msgre/europe/docs/bottom/left_bottom.jpg

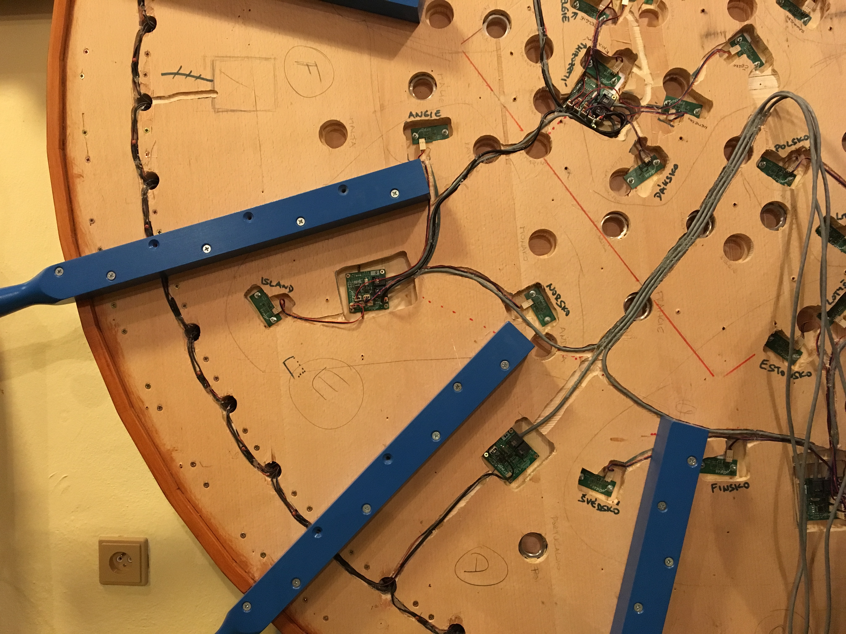
docs/bottom/left_bottom.jpg
