msgre/europe/docs/bottom/left_upper.jpg

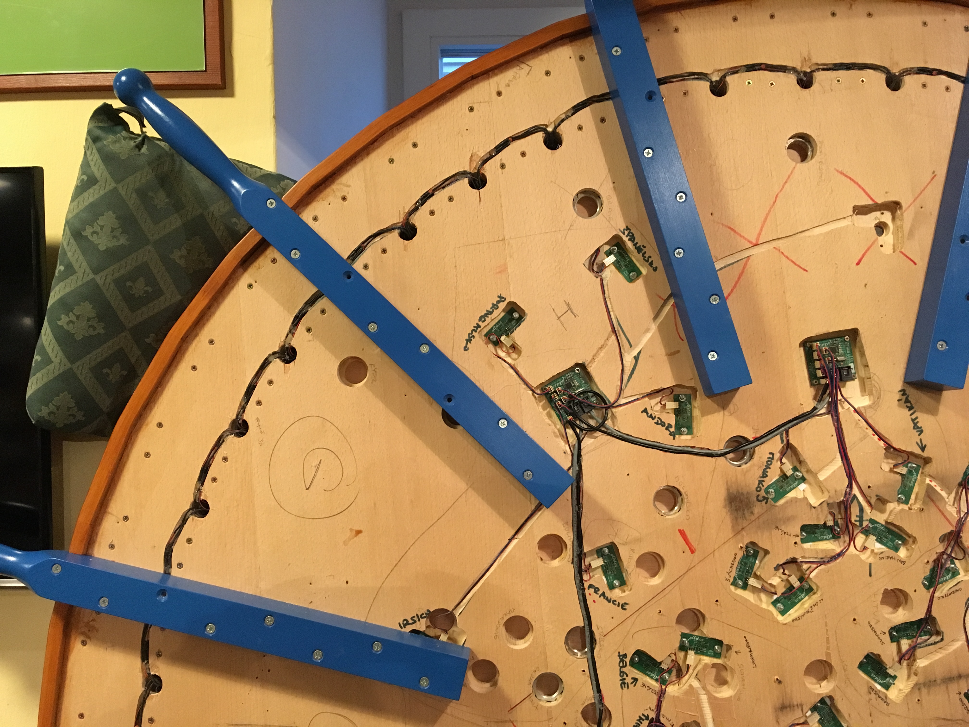
docs/bottom/left_upper.jpg
