msgre/europe/docs/bottom/right_upper.jpg

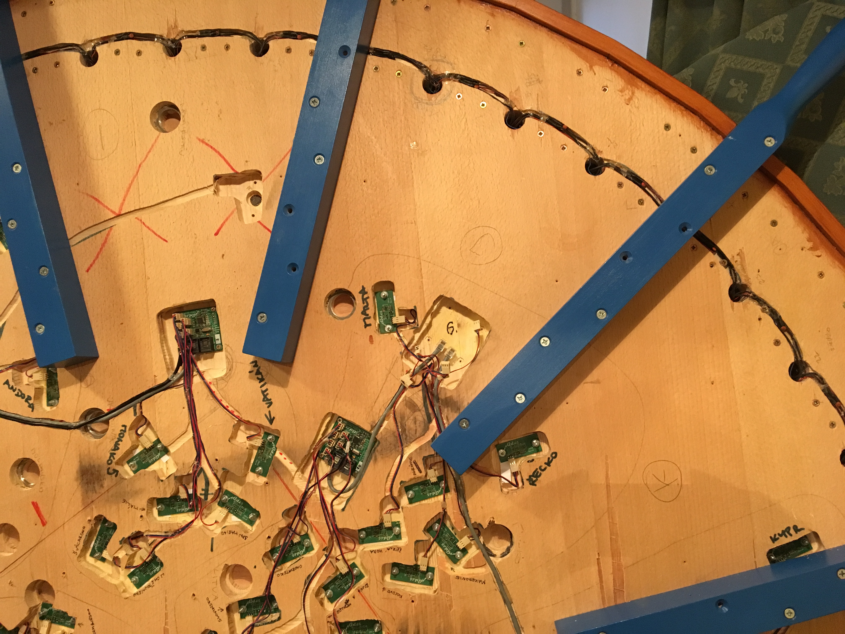
docs/bottom/right_upper.jpg
