msgre/europe/docs/bottom/whole.jpg

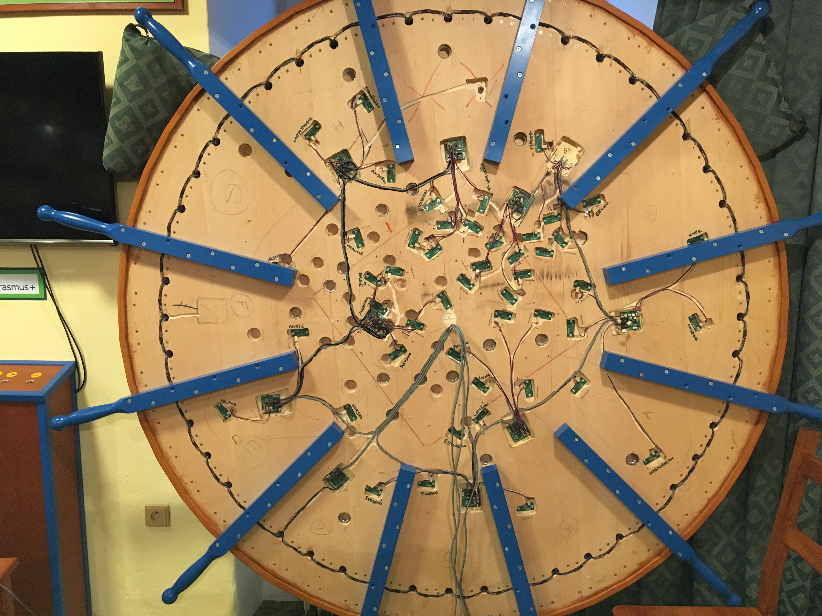
docs/bottom/whole.jpg
