msgre/europe/screenshots/01/01_uvod.png

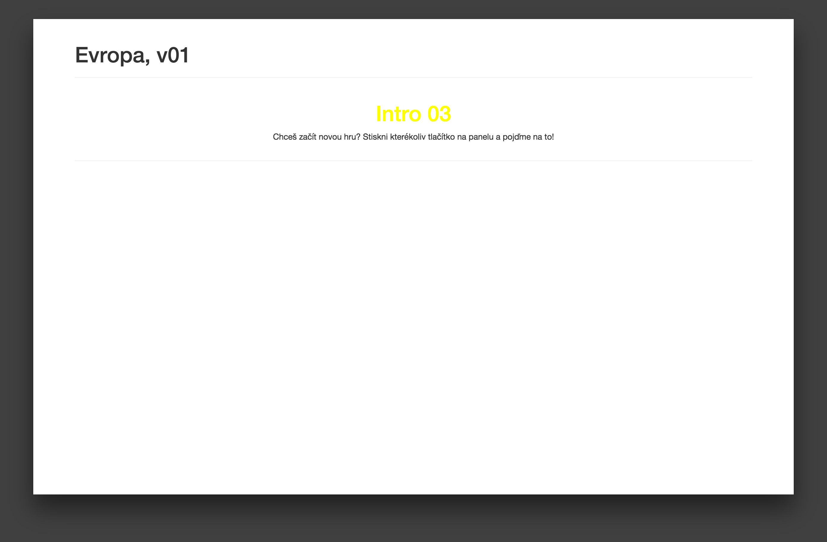
screenshots/01/01_uvod.png
