msgre/europe/screenshots/01/02_kategorie.png

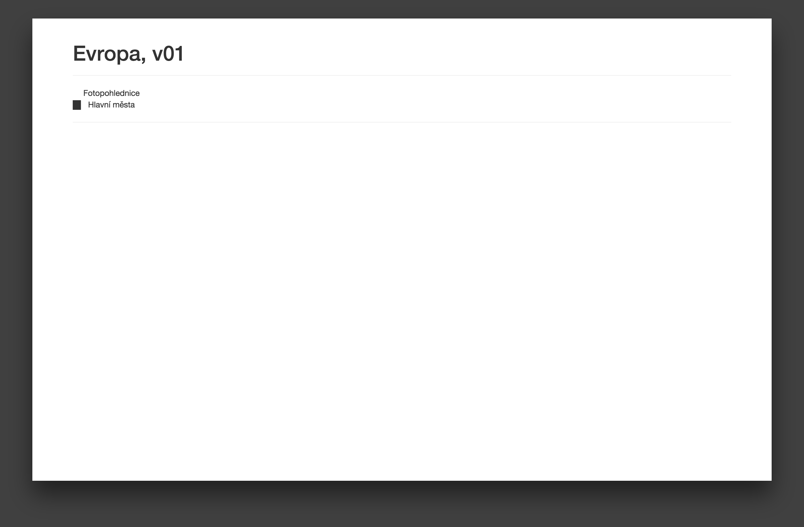
screenshots/01/02_kategorie.png
