msgre/europe/screenshots/01/04_hra.png

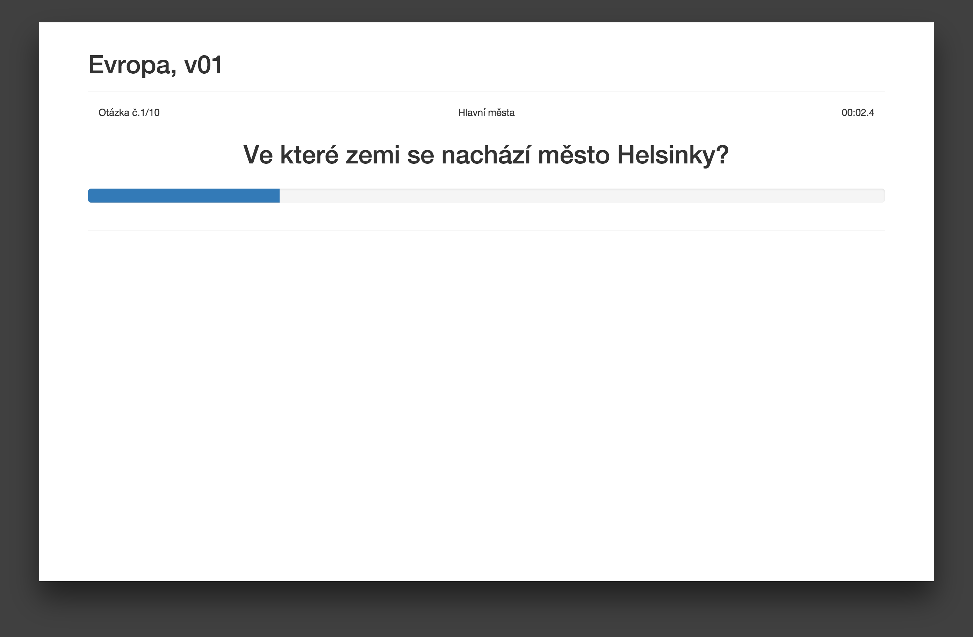
screenshots/01/04_hra.png
