msgre/europe/screenshots/01/05_rekord_1.png

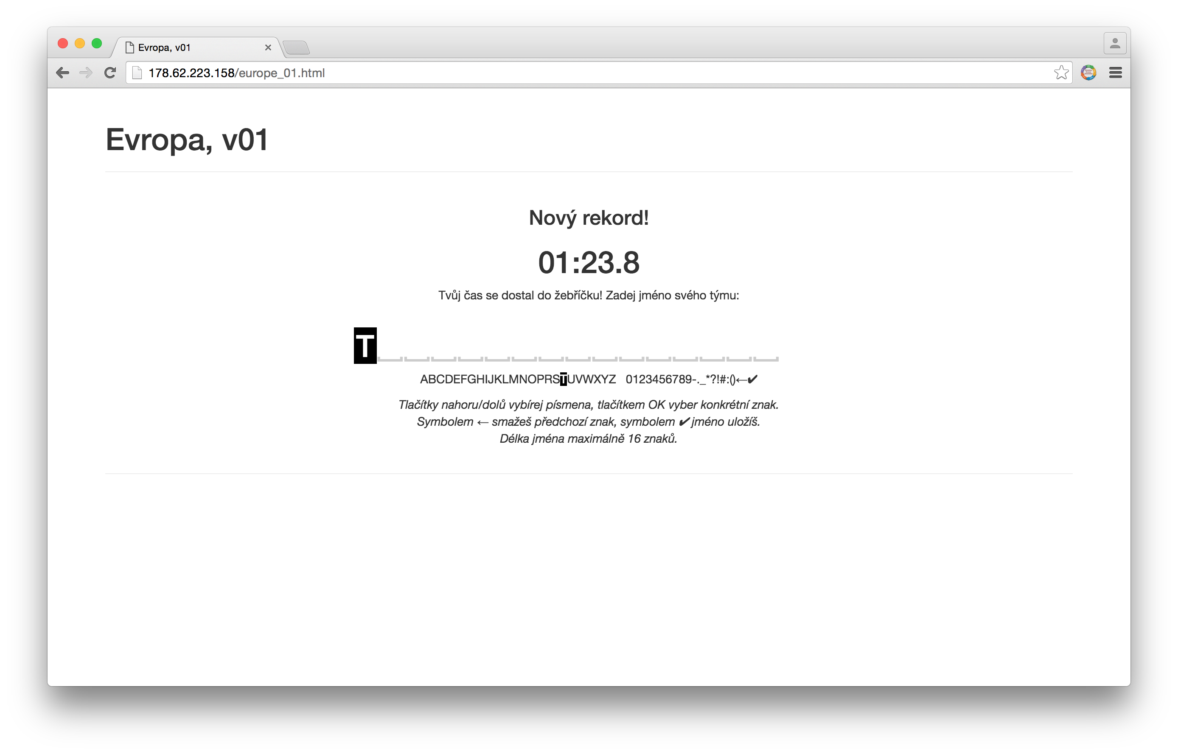
screenshots/01/05_rekord_1.png
