msgre/europe/screenshots/01/06_tabulky.png

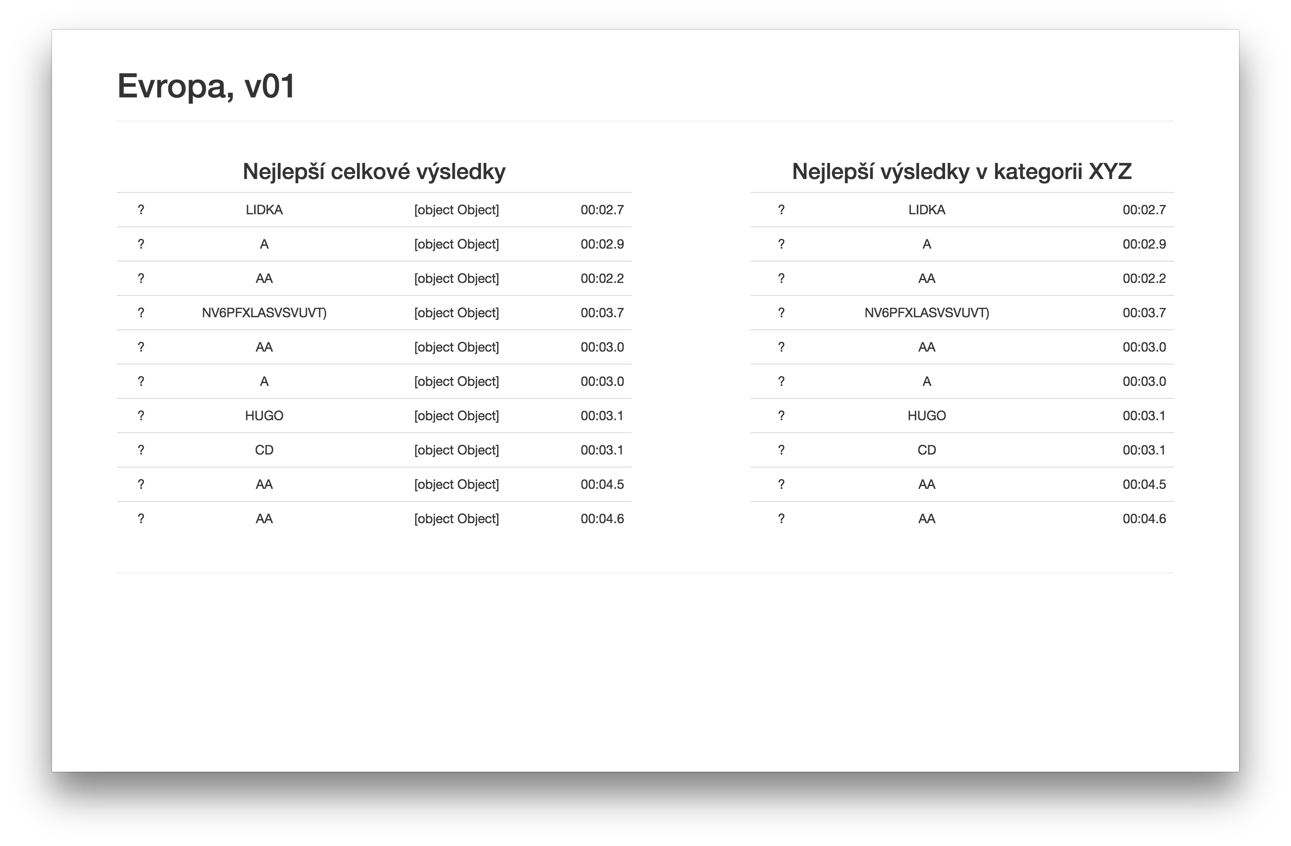
screenshots/01/06_tabulky.png
