msgre/europe/screenshots/02/evropa00.png

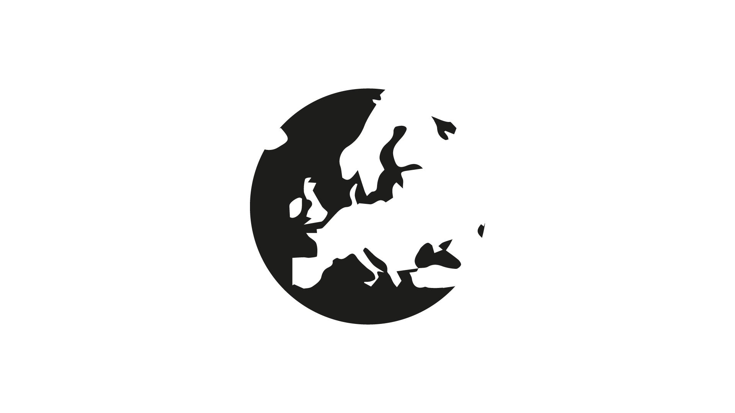
screenshots/02/evropa00.png
