msgre/europe/screenshots/02/evropa01.png

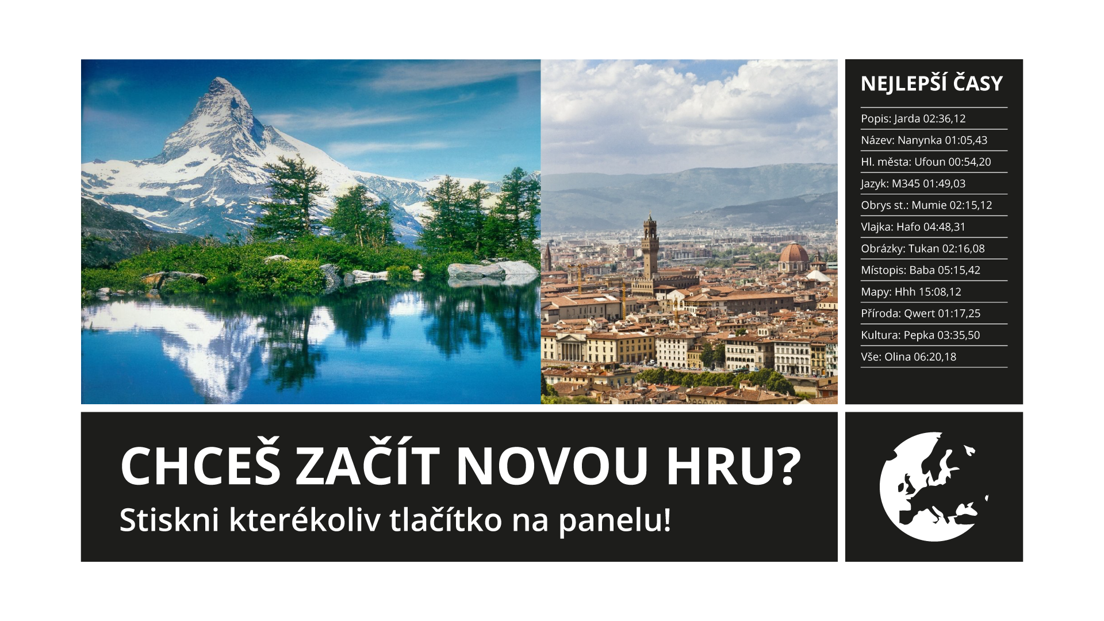
screenshots/02/evropa01.png
