msgre/europe/screenshots/02/evropa02.png

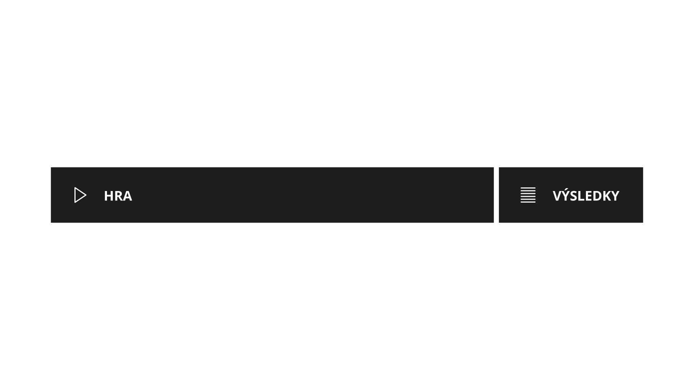
screenshots/02/evropa02.png
