msgre/europe/screenshots/02/evropa03.png

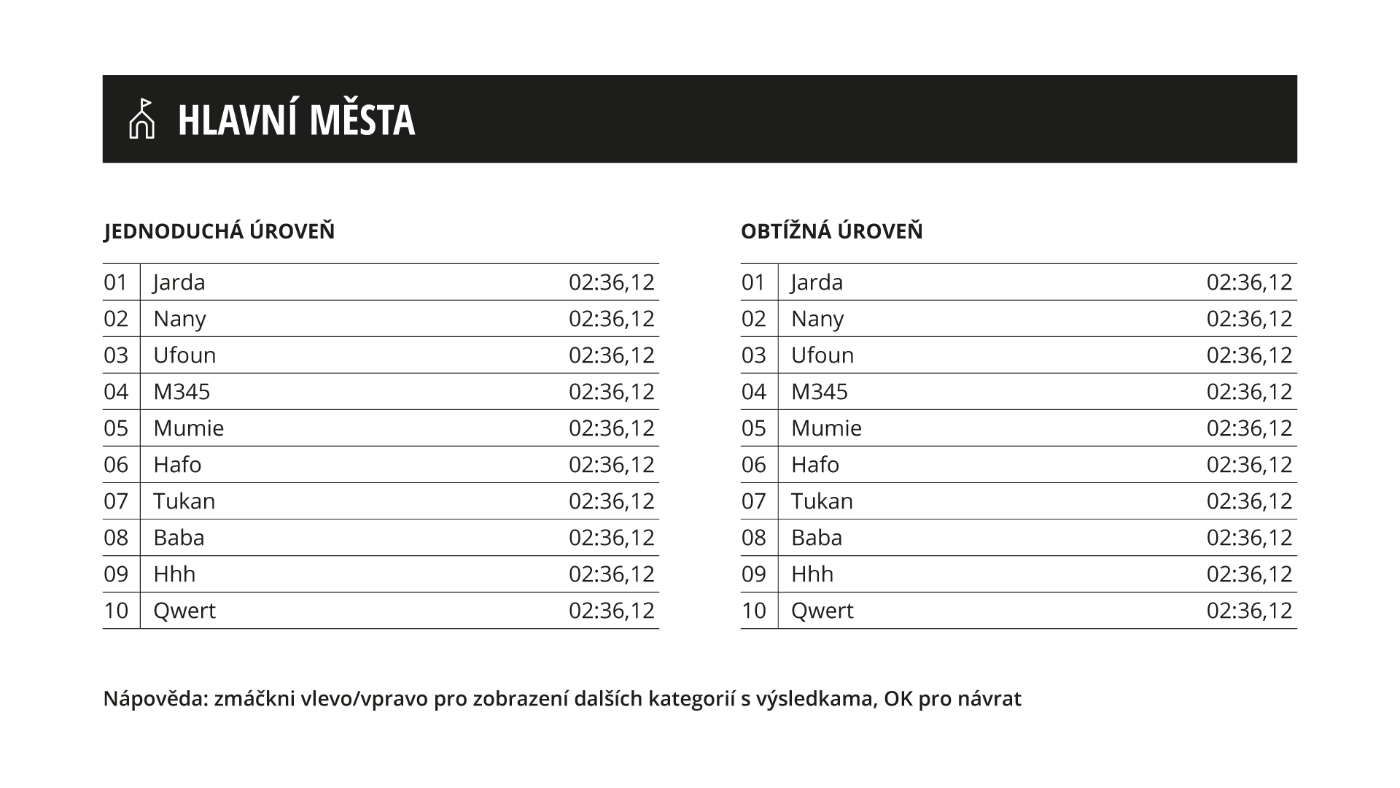
screenshots/02/evropa03.png
