msgre/europe/screenshots/02/evropa04.png

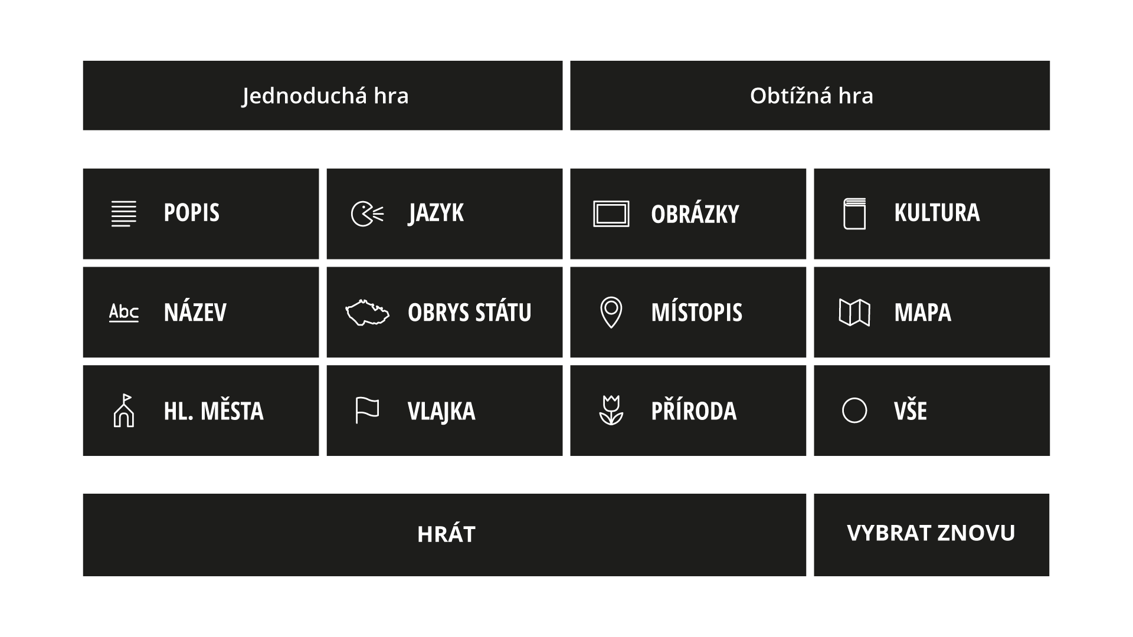
screenshots/02/evropa04.png
