msgre/europe/screenshots/02/evropa05a.png

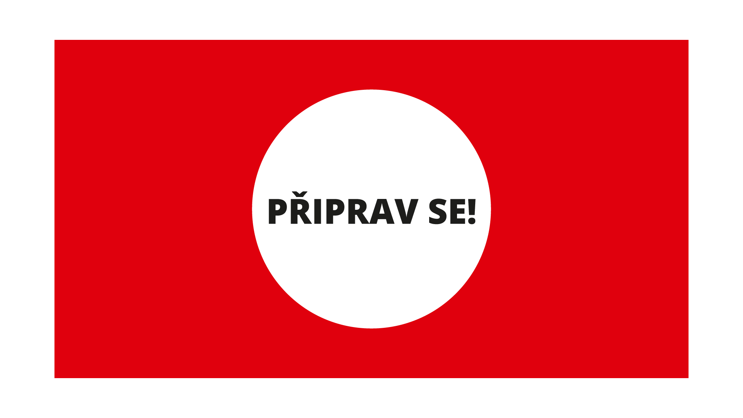
screenshots/02/evropa05a.png
