msgre/europe/screenshots/02/evropa05b.png

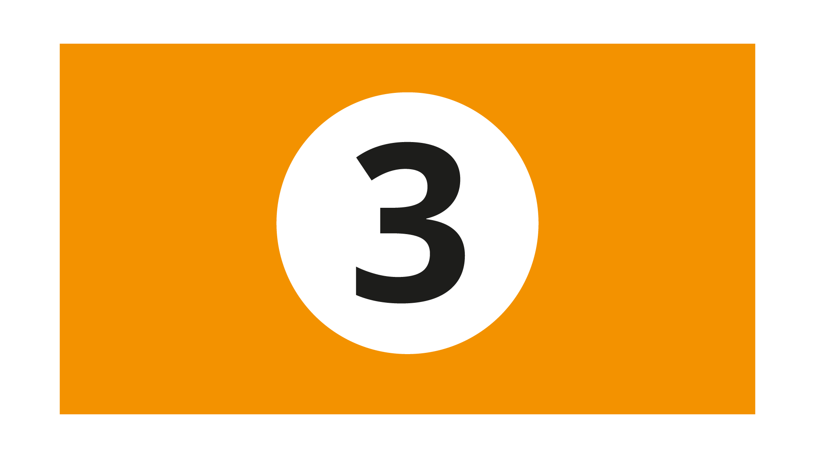
screenshots/02/evropa05b.png
