msgre/europe/screenshots/02/evropa06a.png

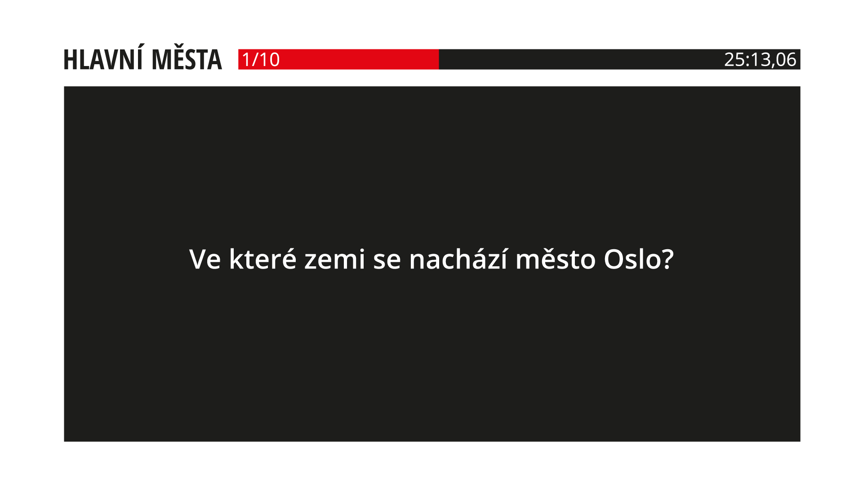
screenshots/02/evropa06a.png
