msgre/europe/screenshots/02/evropa06b.png

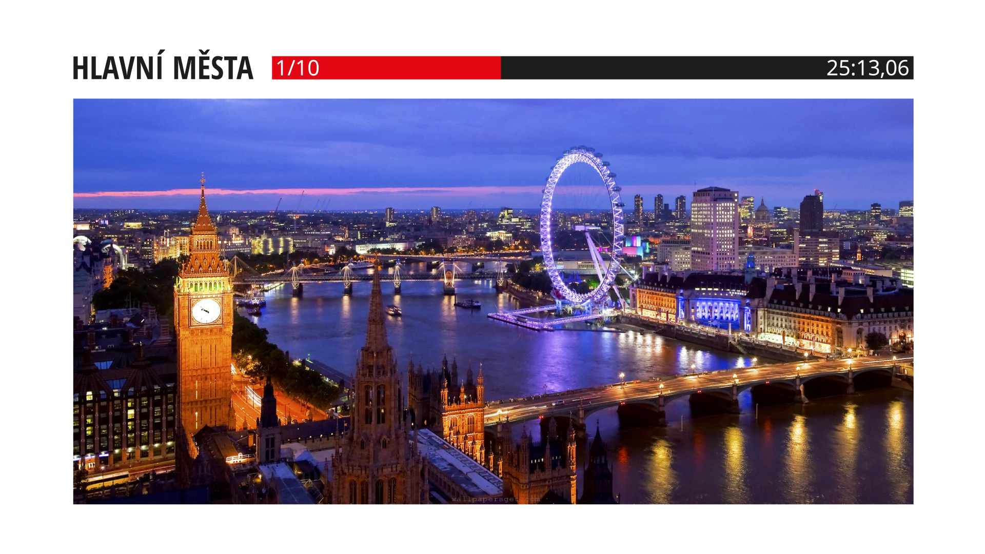
screenshots/02/evropa06b.png
