msgre/europe/screenshots/02/evropa06c.png

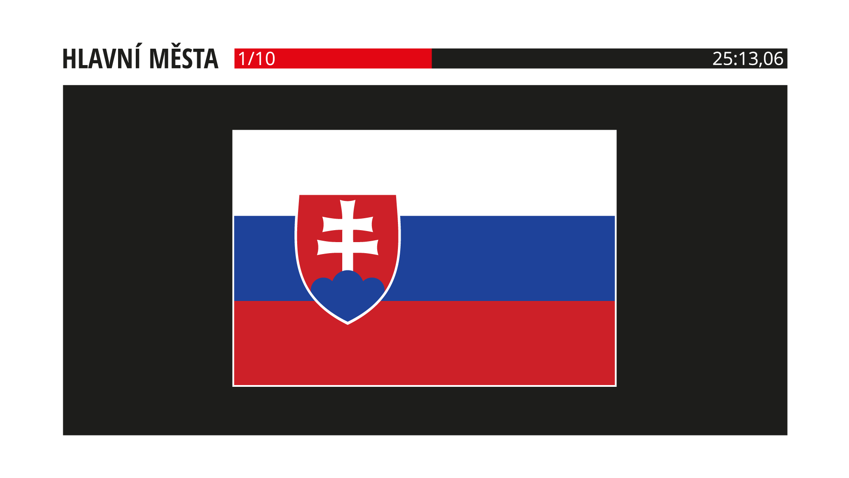
screenshots/02/evropa06c.png
