msgre/europe/screenshots/02/evropa06d.png

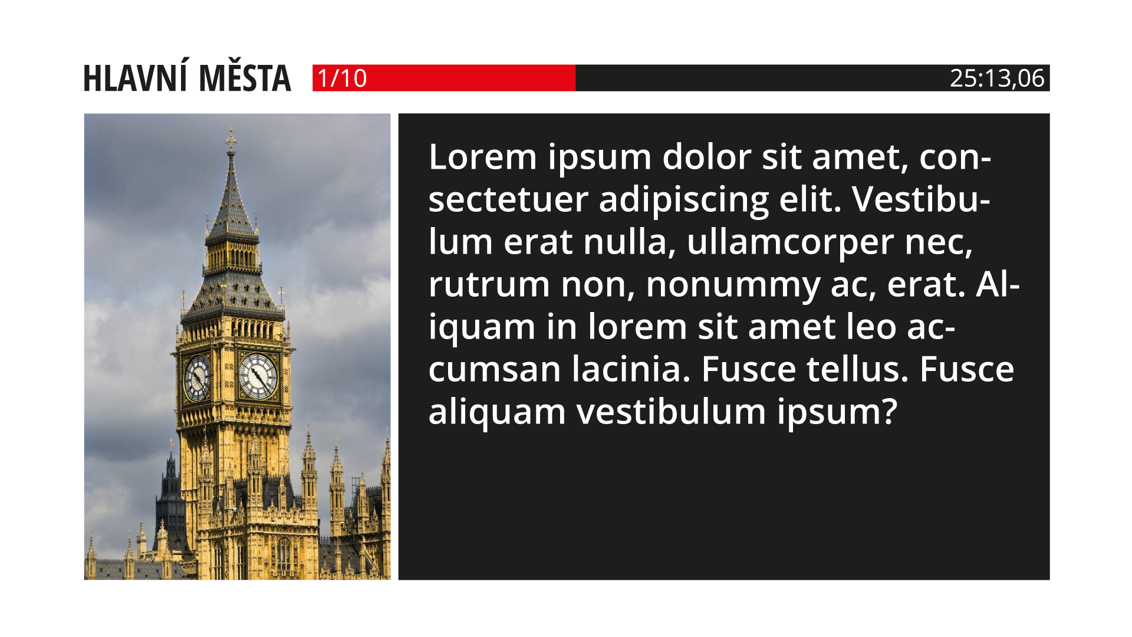
screenshots/02/evropa06d.png
