msgre/europe/screenshots/02/evropa07.png

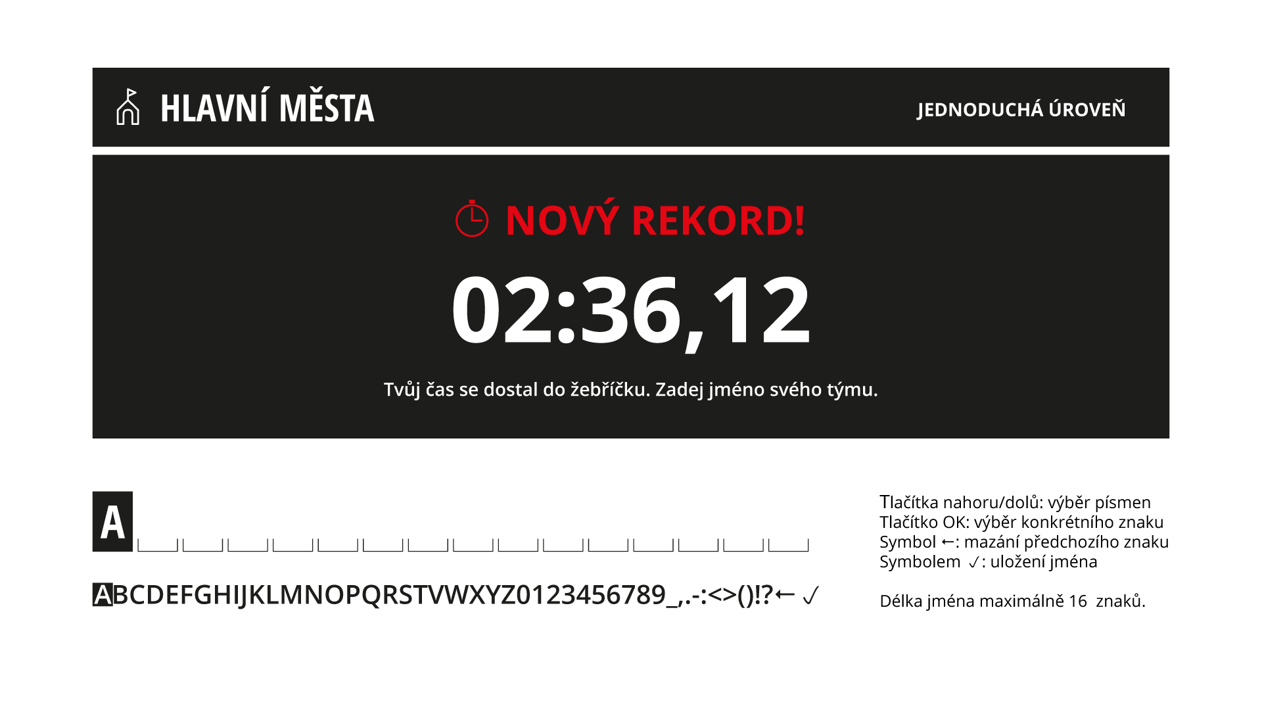
screenshots/02/evropa07.png
