msgre/europe/screenshots/02/evropa08.png

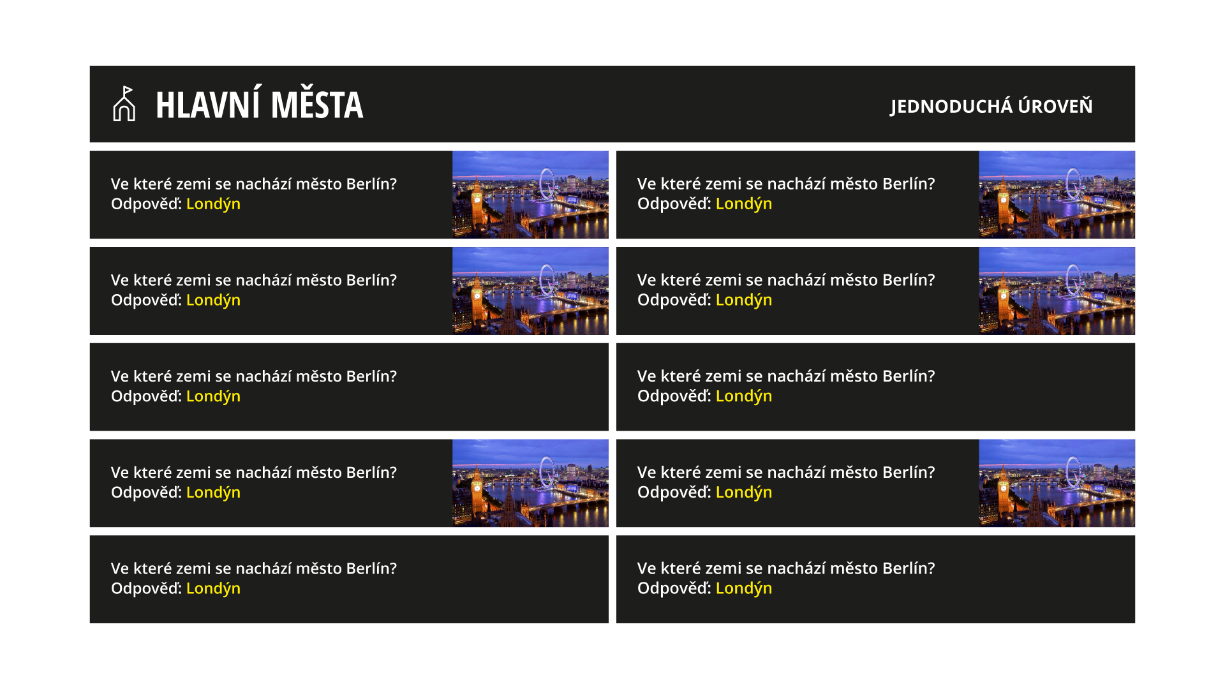
screenshots/02/evropa08.png
