msgre/europe/screenshots/02/evropa09.png

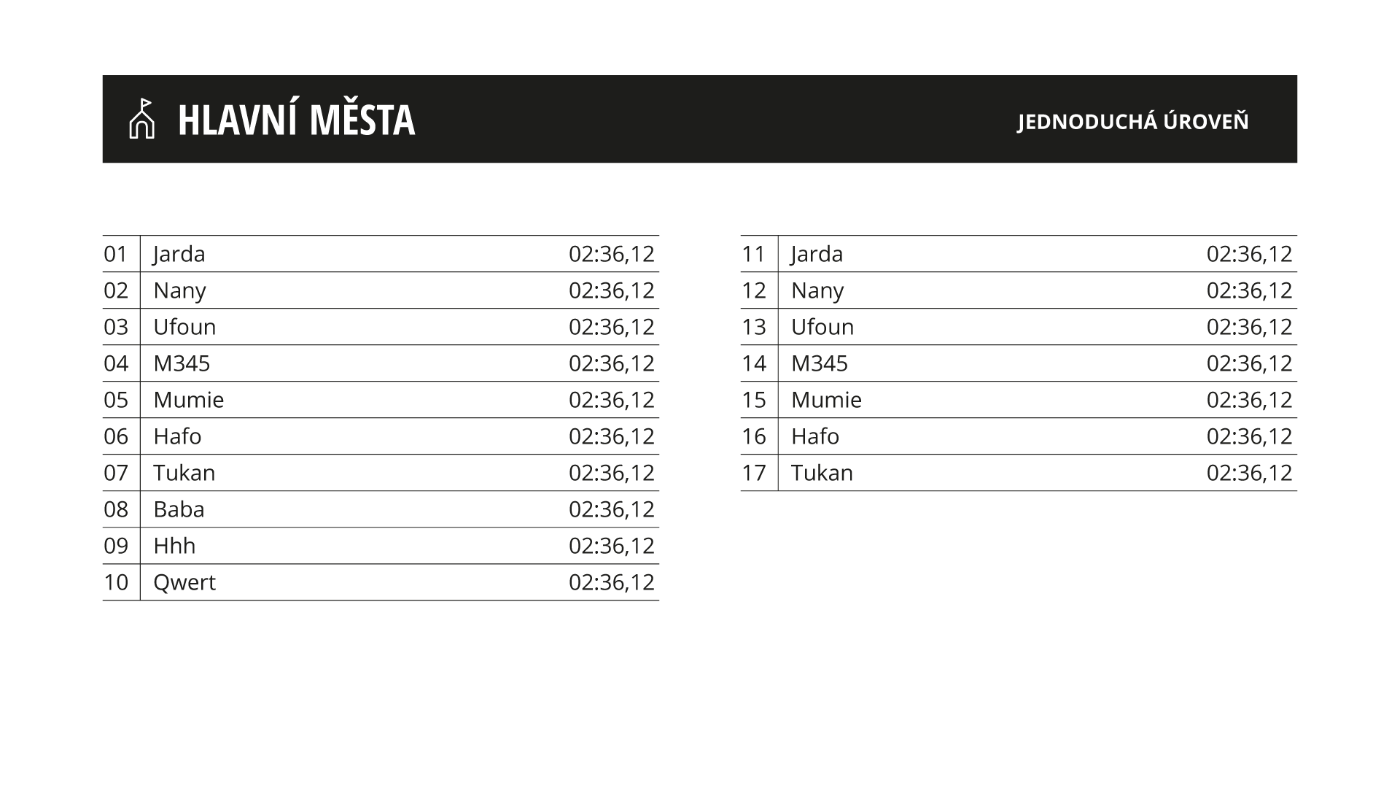
screenshots/02/evropa09.png
