msgre/europe/screenshots/03/foto-2_3.png

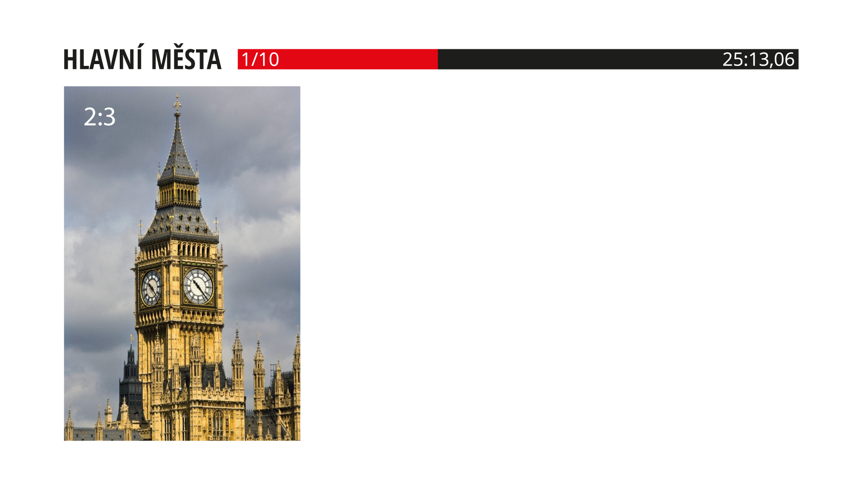
screenshots/03/foto-2_3.png
