msgre/europe/screenshots/03/foto-3_2.png

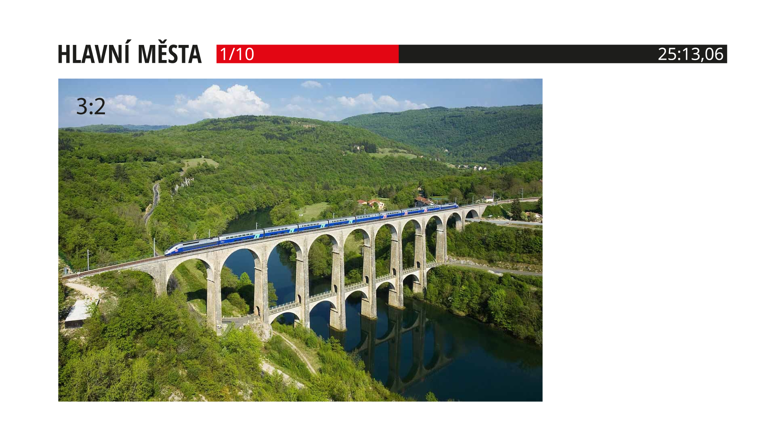
screenshots/03/foto-3_2.png
