msgre/europe/screenshots/03/foto-16_9-full.png

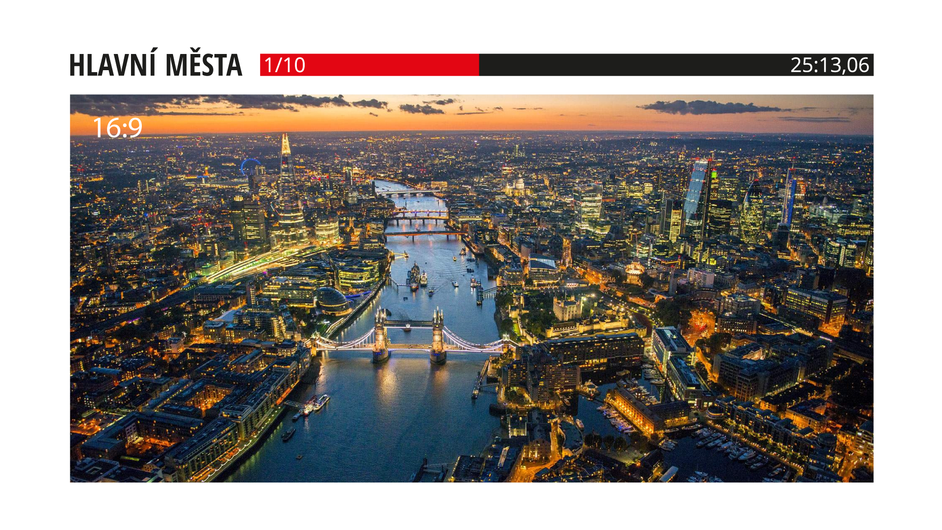
screenshots/03/foto-16_9-full.png
