msgre/europe/screenshots/03/foto-16_9.png

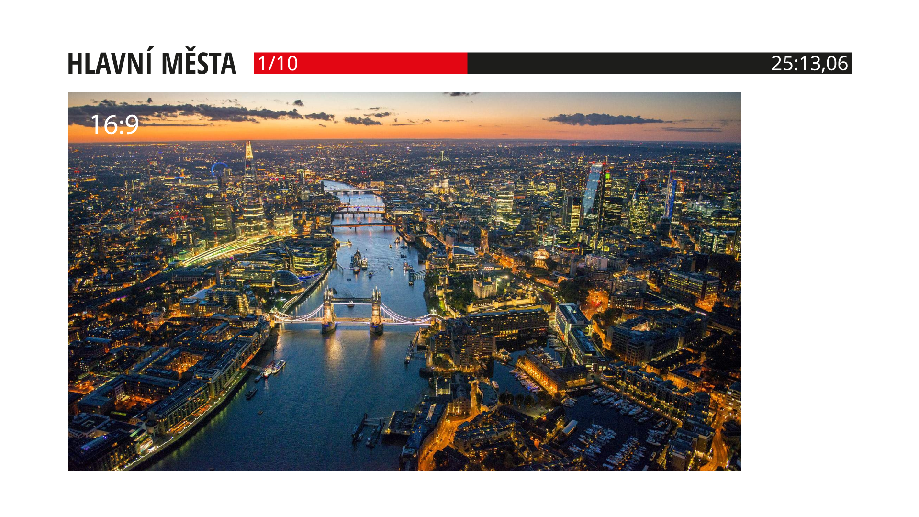
screenshots/03/foto-16_9.png
