msgre/europe/screenshots/03/foto-text-1_1.png

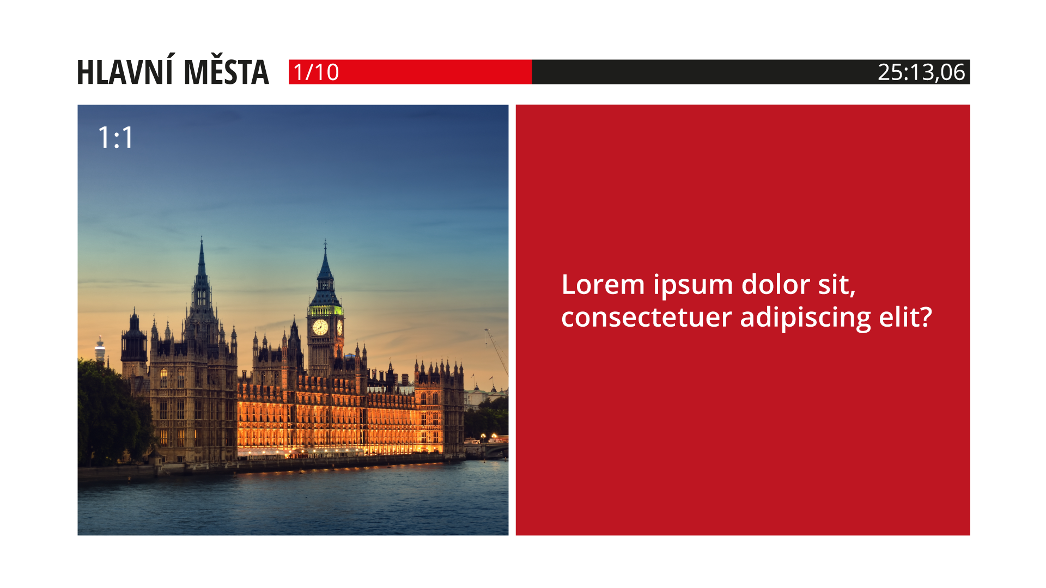
screenshots/03/foto-text-1_1.png
