msgre/europe/screenshots/03/foto-text-2_3.png

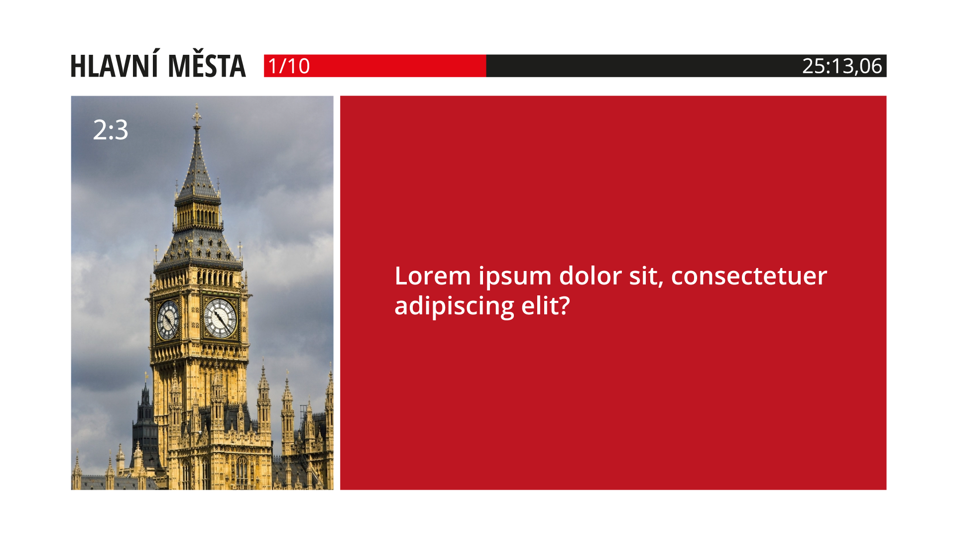
screenshots/03/foto-text-2_3.png
