msgre/europe/screenshots/03/foto-text-3_2.png

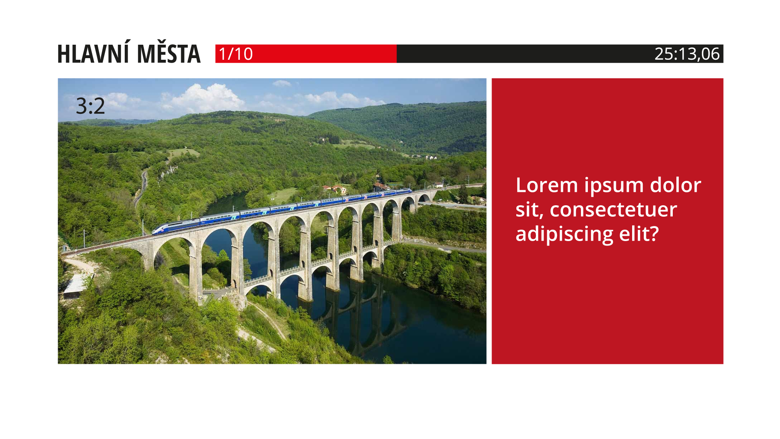
screenshots/03/foto-text-3_2.png
