msgre/europe/screenshots/03/foto-text-3_4.png

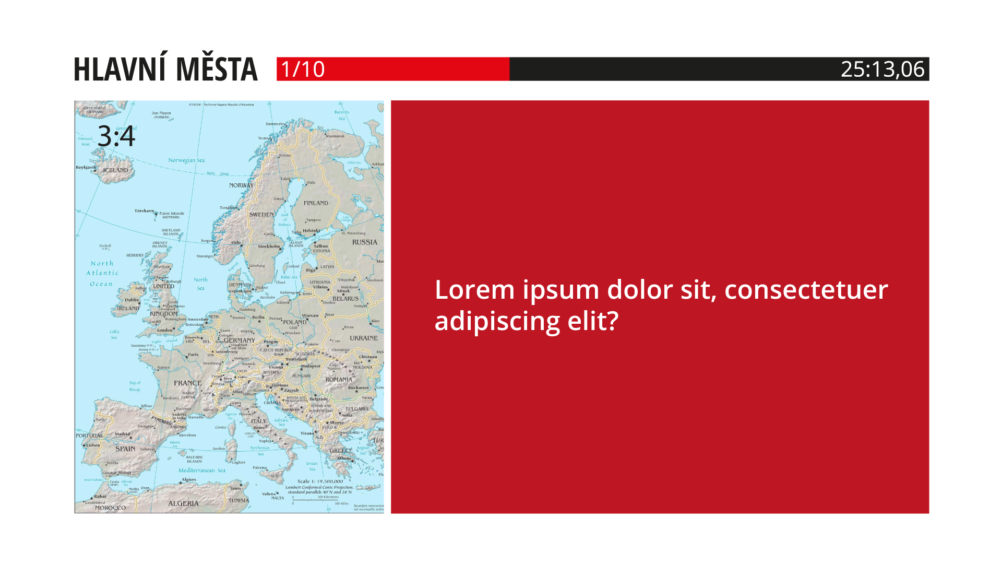
screenshots/03/foto-text-3_4.png
