msgre/europe/screenshots/03/foto-text-4_3.png

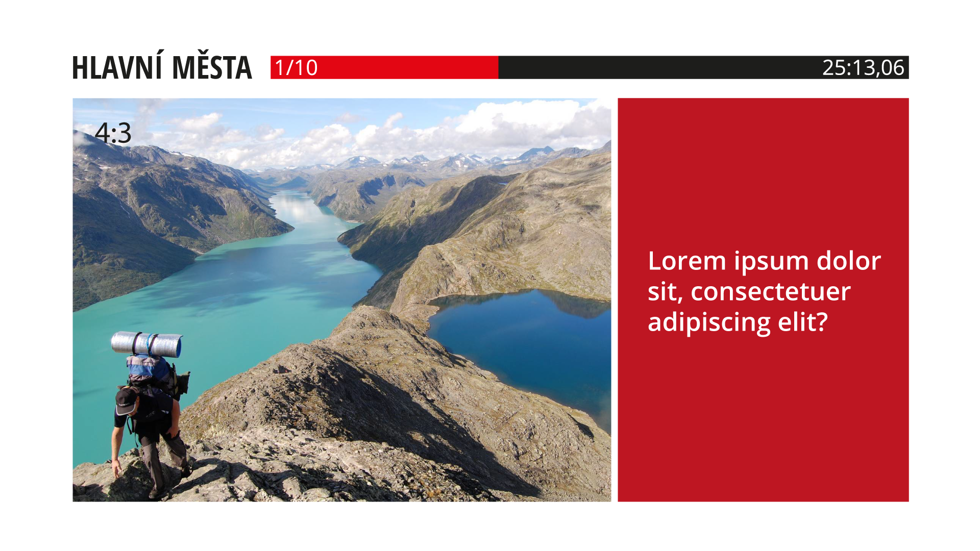
screenshots/03/foto-text-4_3.png
