msgre/europe/screenshots/03/foto-text-9_16.png

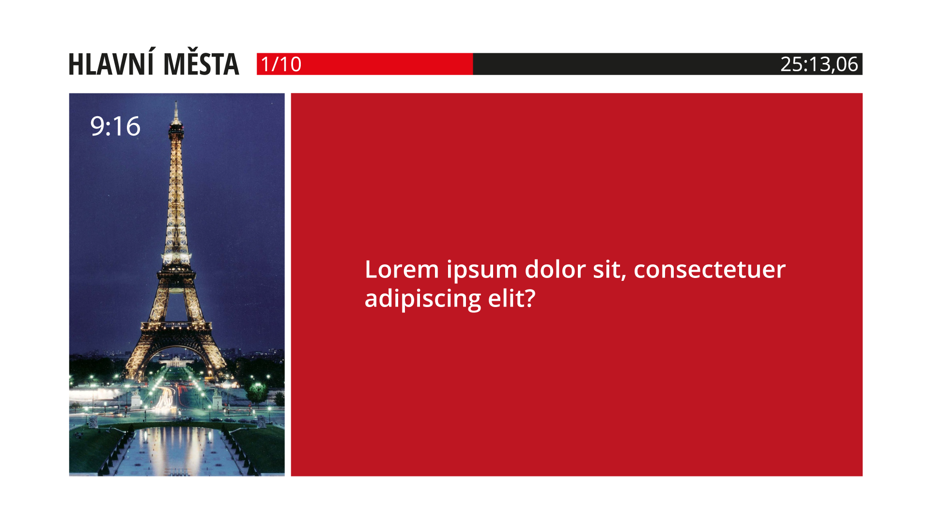
screenshots/03/foto-text-9_16.png
