msgre/europe/screenshots/03/foto-text-16_9.png

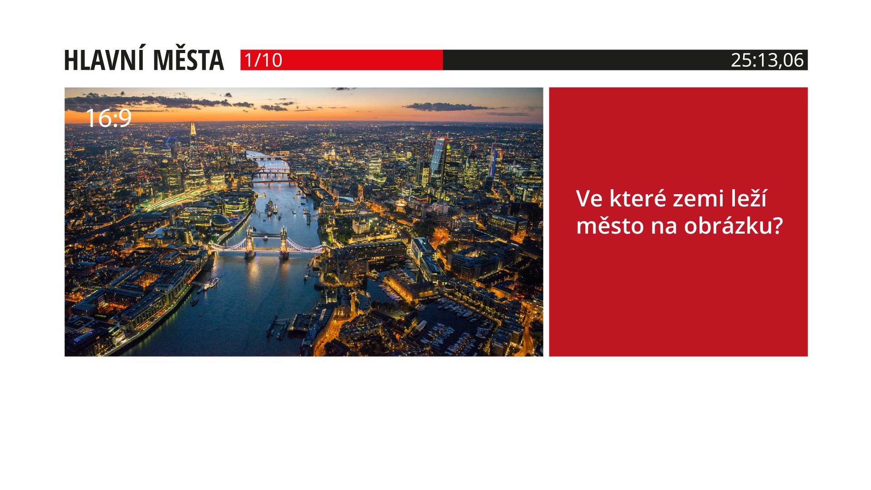
screenshots/03/foto-text-16_9.png
