msgre/europe/screenshots/03/obrys-statu.png

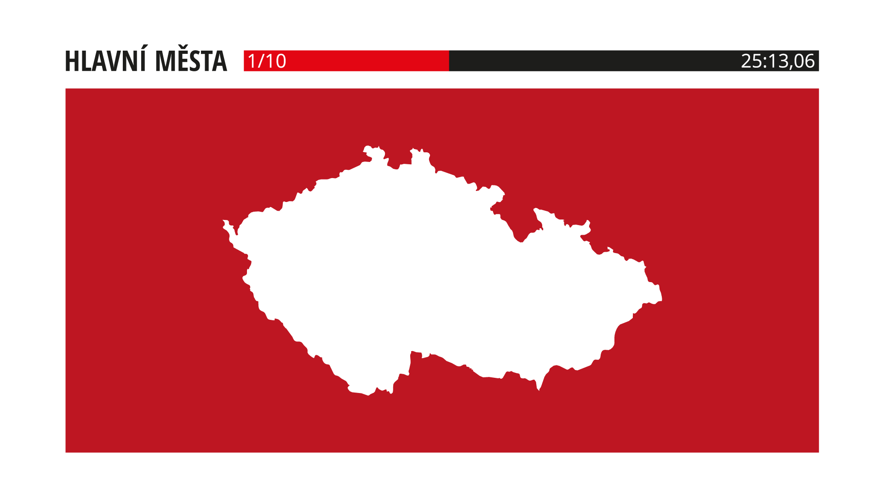
screenshots/03/obrys-statu.png
