msgre/europe/screenshots/03/only-text.png

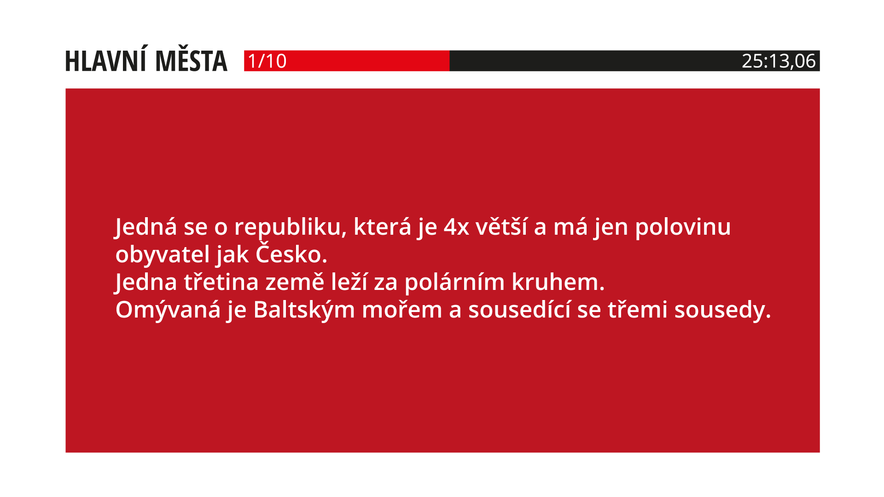
screenshots/03/only-text.png
