msgre/europe/screenshots/04/dosazeny-cas01.png

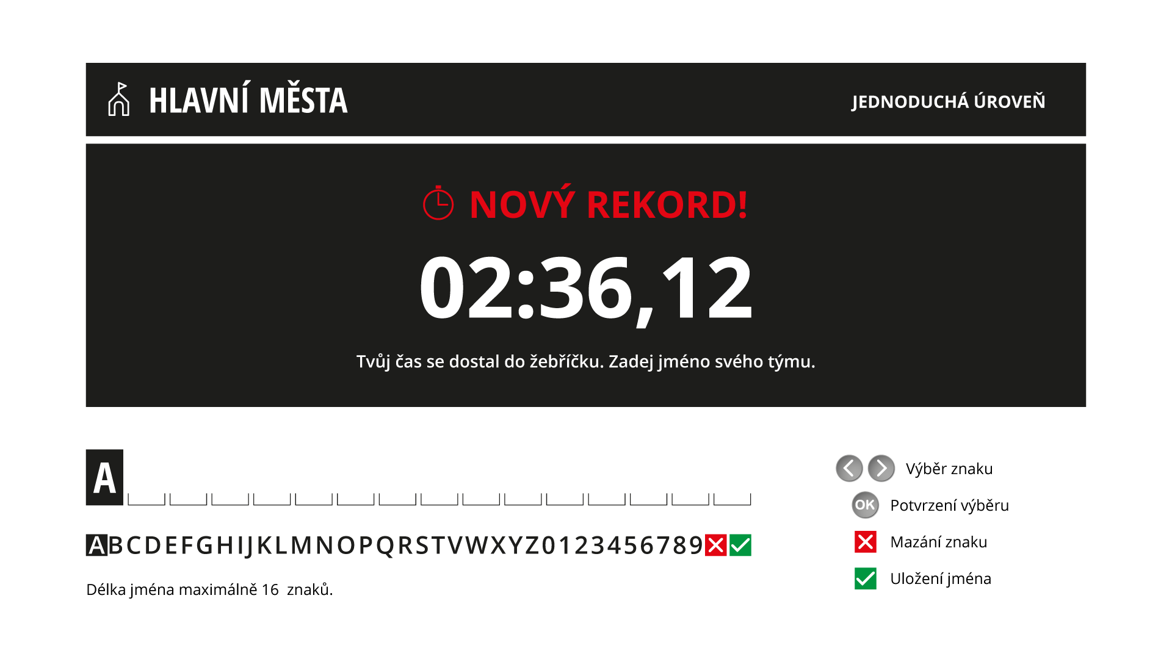
screenshots/04/dosazeny-cas01.png
