msgre/europe/screenshots/04/dosazeny-cas02.png

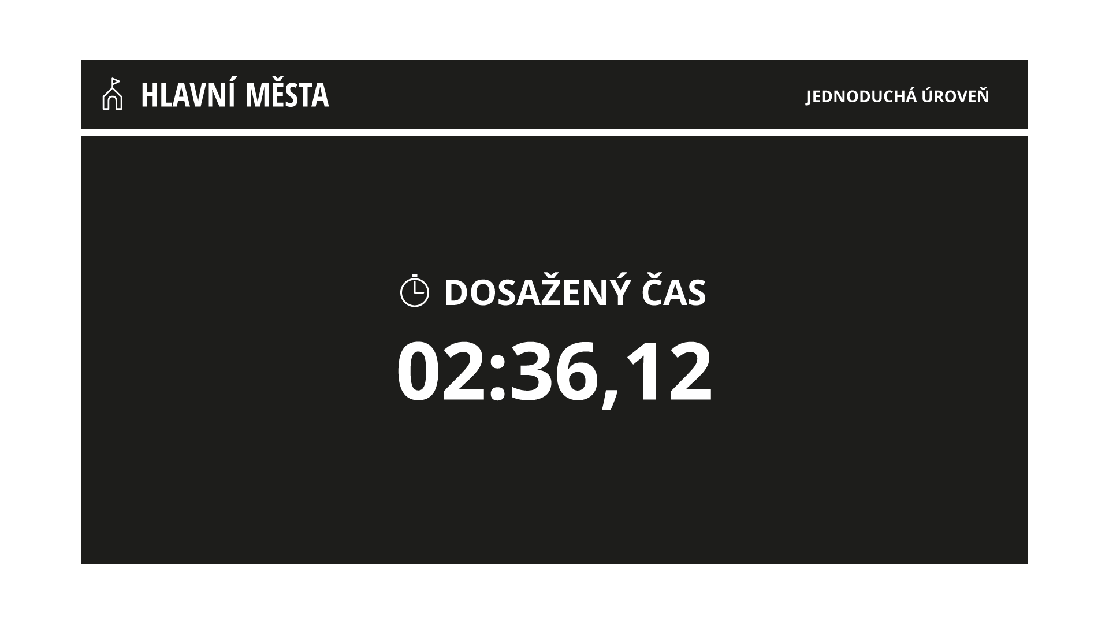
screenshots/04/dosazeny-cas02.png
