msgre/europe/screenshots/04/kategorie.png

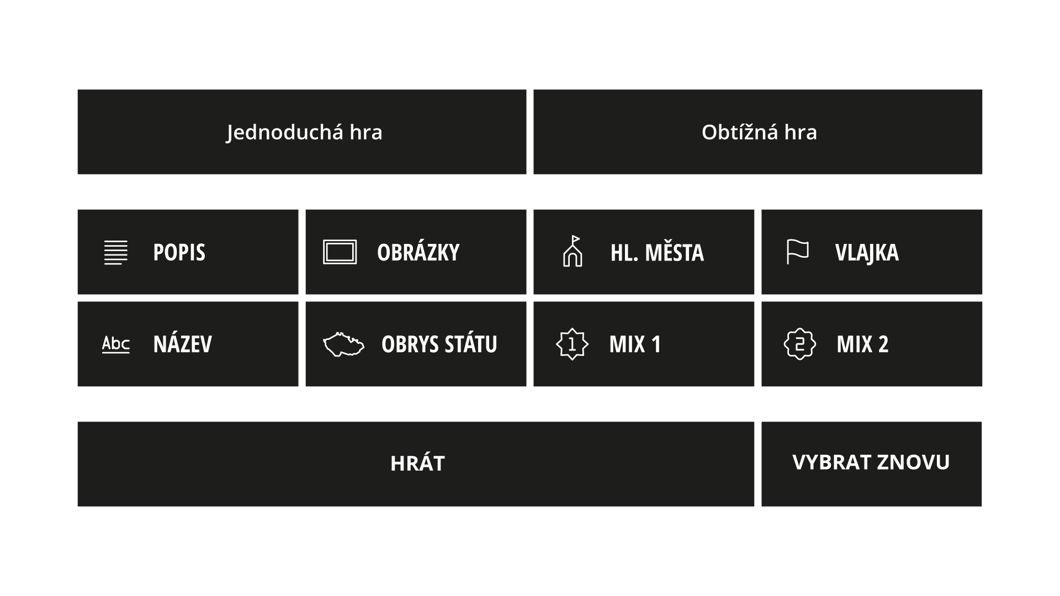
screenshots/04/kategorie.png
