msgre/europe/screenshots/04/odpovedi01.png

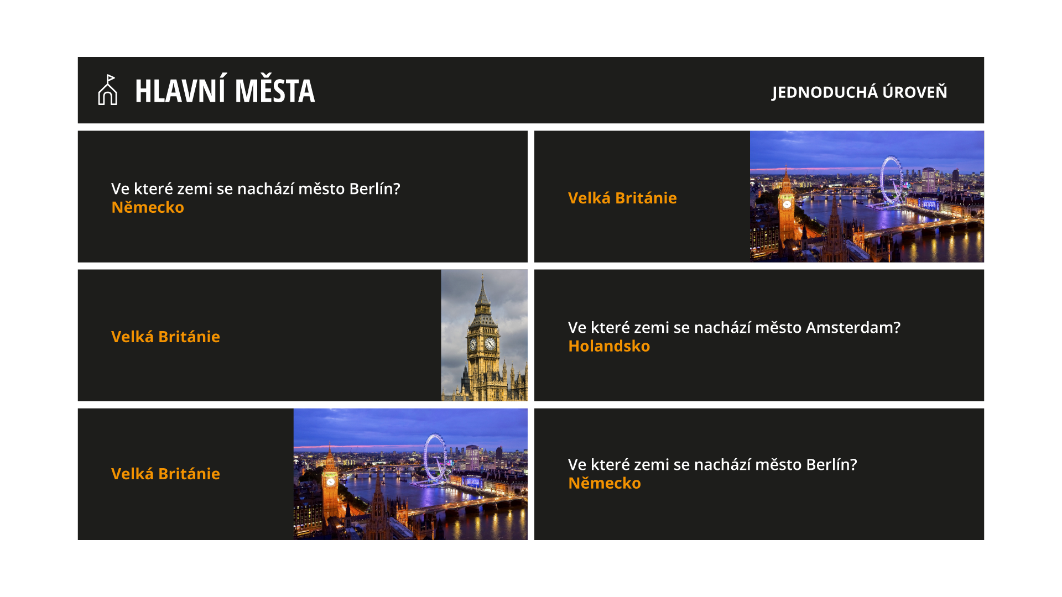
screenshots/04/odpovedi01.png
