msgre/europe/screenshots/04/odpovedi02.png

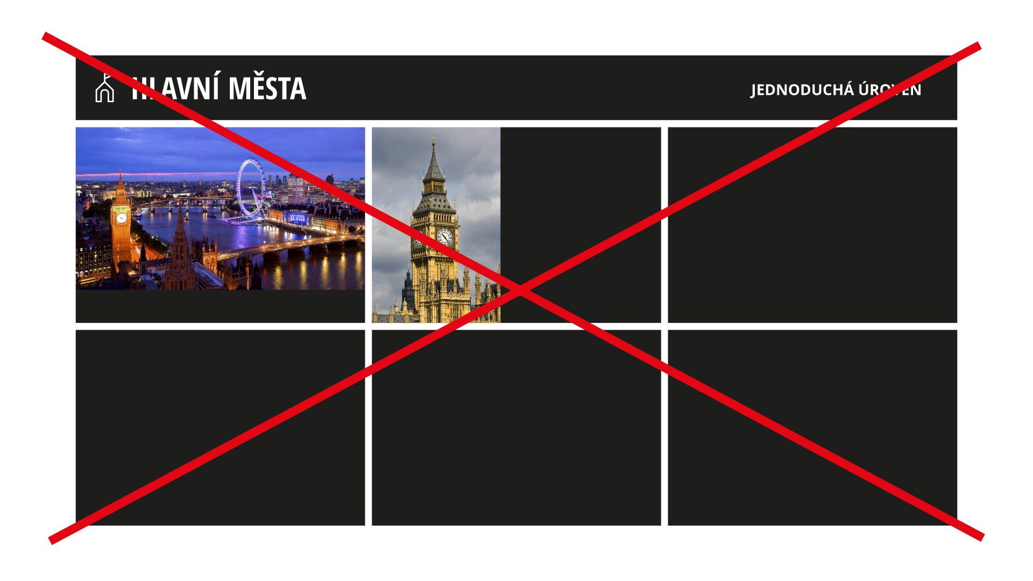
screenshots/04/odpovedi02.png
