msgre/europe/screenshots/06/game1.png

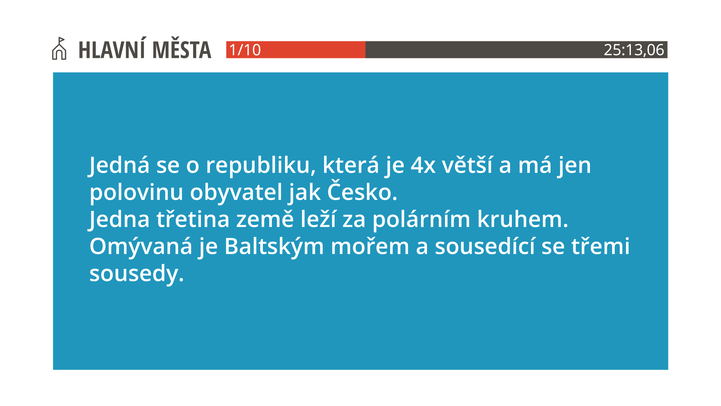
screenshots/06/game1.png
