msgre/europe/screenshots/06/game2.png

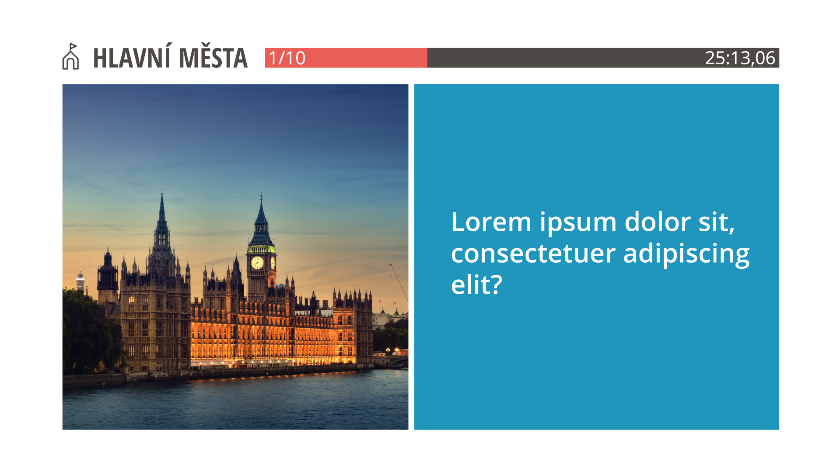
screenshots/06/game2.png
