msgre/europe/screenshots/06/game4.png

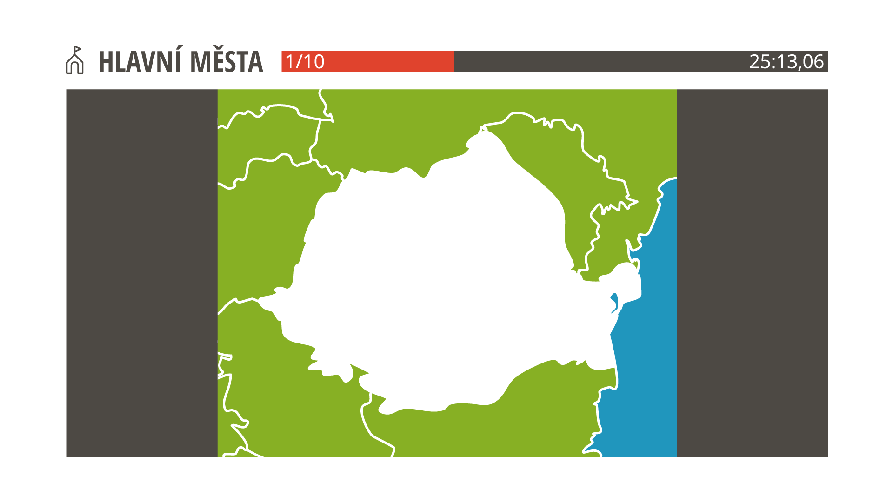
screenshots/06/game4.png
