msgre/europe/screenshots/06/game5.png

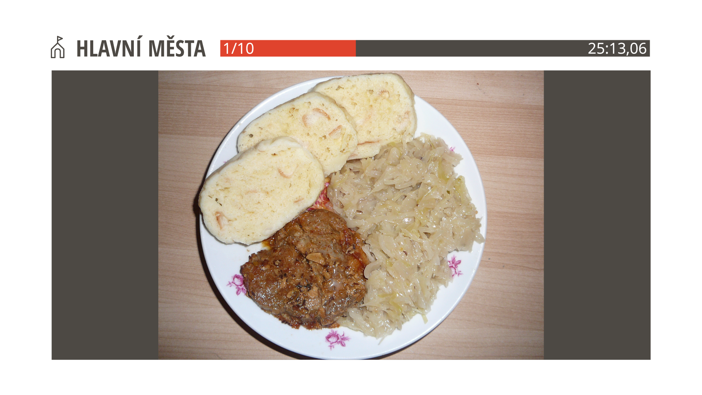
screenshots/06/game5.png
