msgre/europe/screenshots/06/gamemode.png

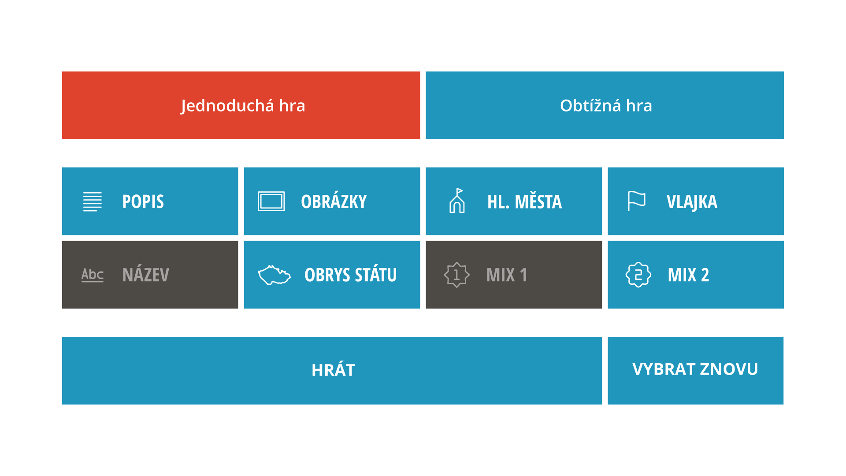
screenshots/06/gamemode.png
