msgre/europe/screenshots/06/intro.png

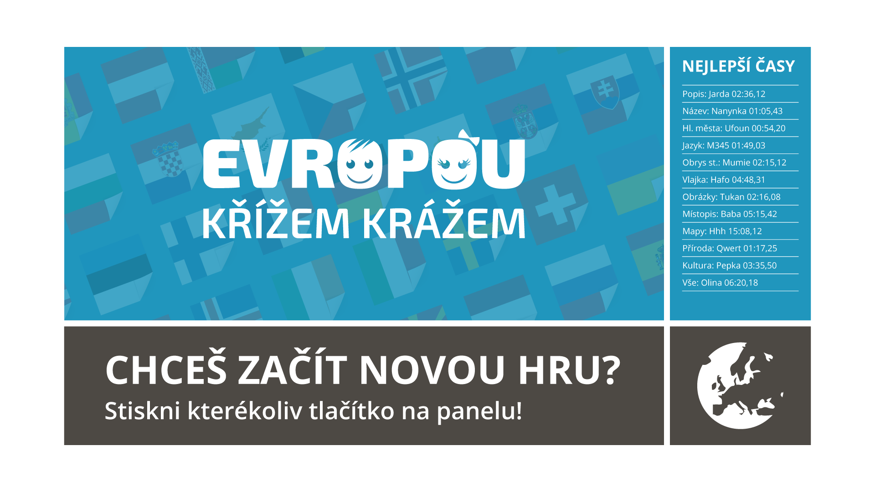
screenshots/06/intro.png
