msgre/europe/screenshots/06/mapa.png

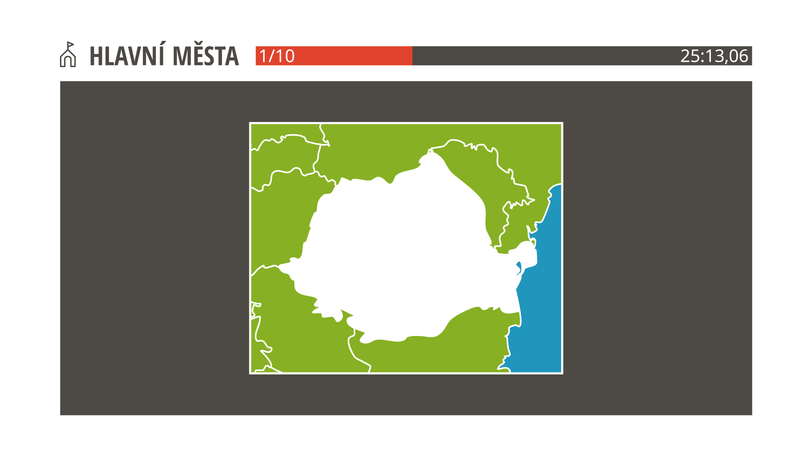
screenshots/06/mapa.png
