msgre/europe/screenshots/06/recap.png

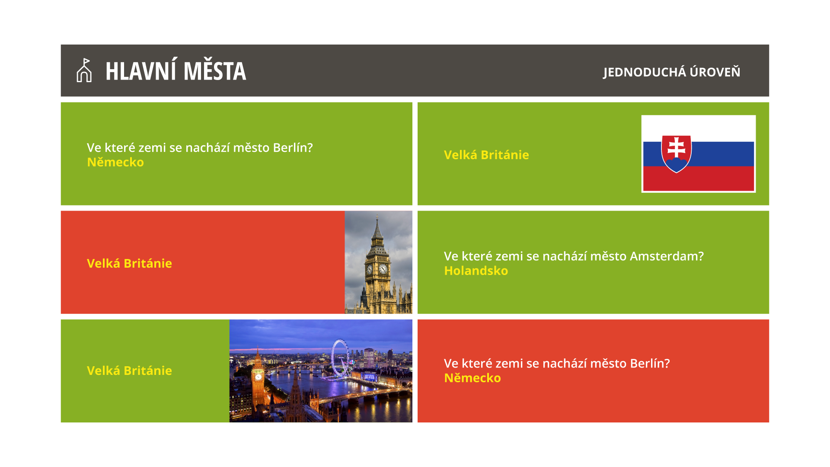
screenshots/06/recap.png
