msgre/europe/screenshots/06/titul2.png

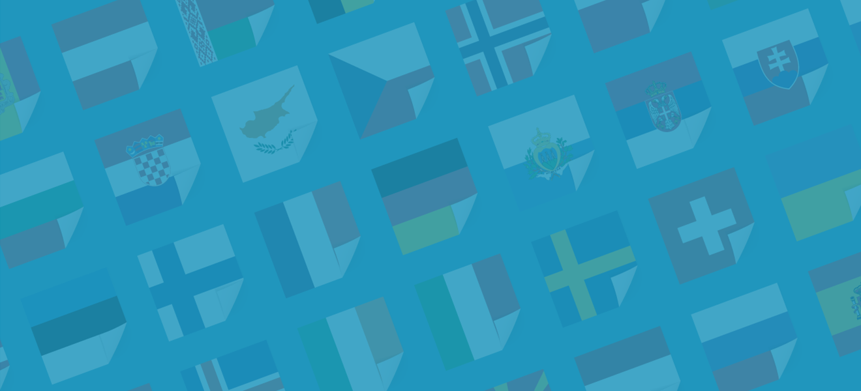
screenshots/06/titul2.png
