msgre/europe/static/foto-1_1.jpg

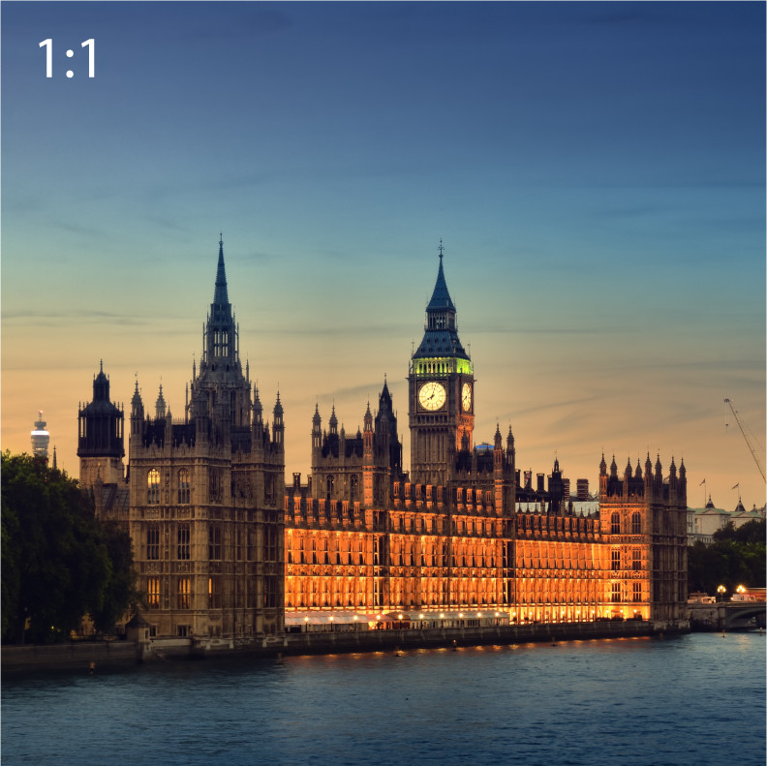
static/foto-1_1.jpg
