msgre/europe/static/foto-2_3.jpg

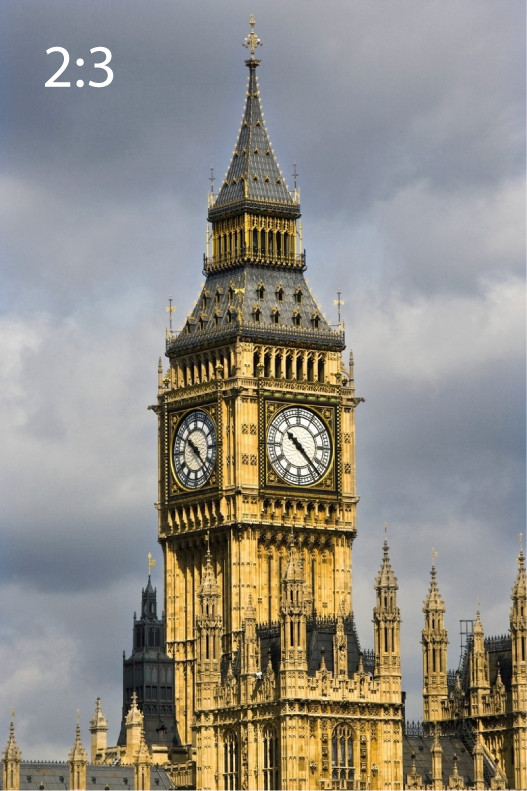
static/foto-2_3.jpg
