msgre/europe/static/foto-3_4.jpg

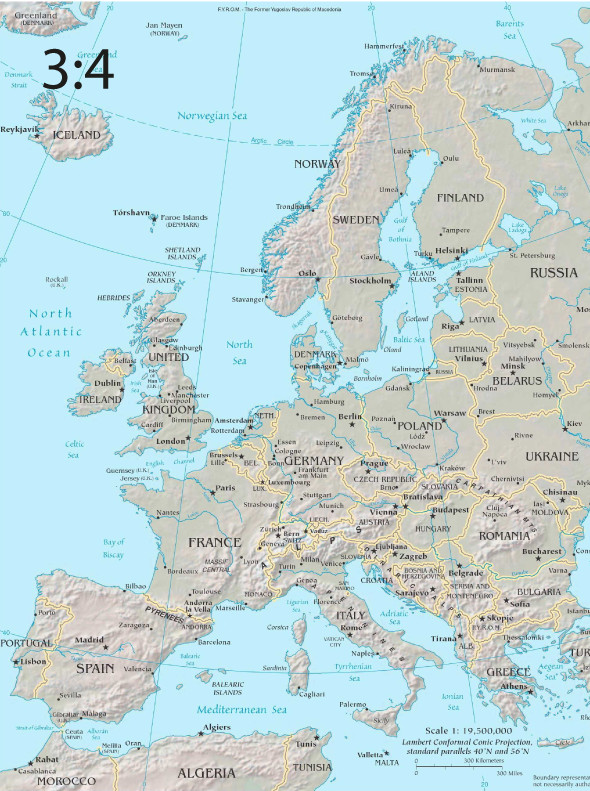
static/foto-3_4.jpg
