msgre/europe/static/foto-4_3.jpg

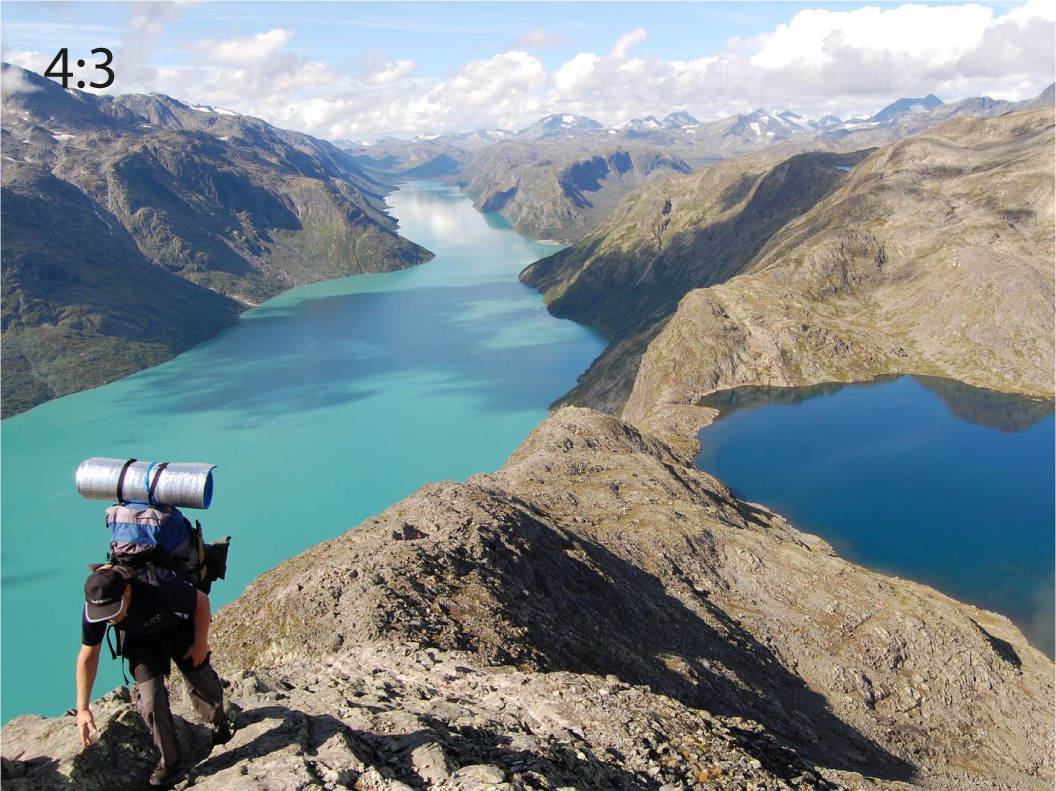
static/foto-4_3.jpg
