msgre/europe/static/foto-9_16.jpg

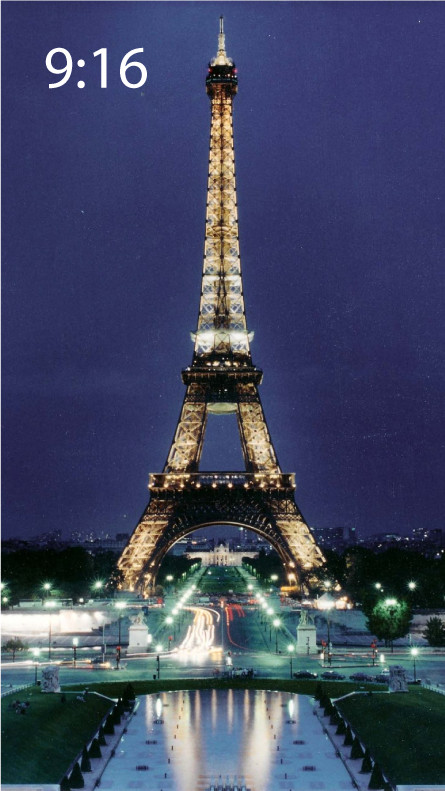
static/foto-9_16.jpg
