msgre/europe/static/foto-16_9.jpg

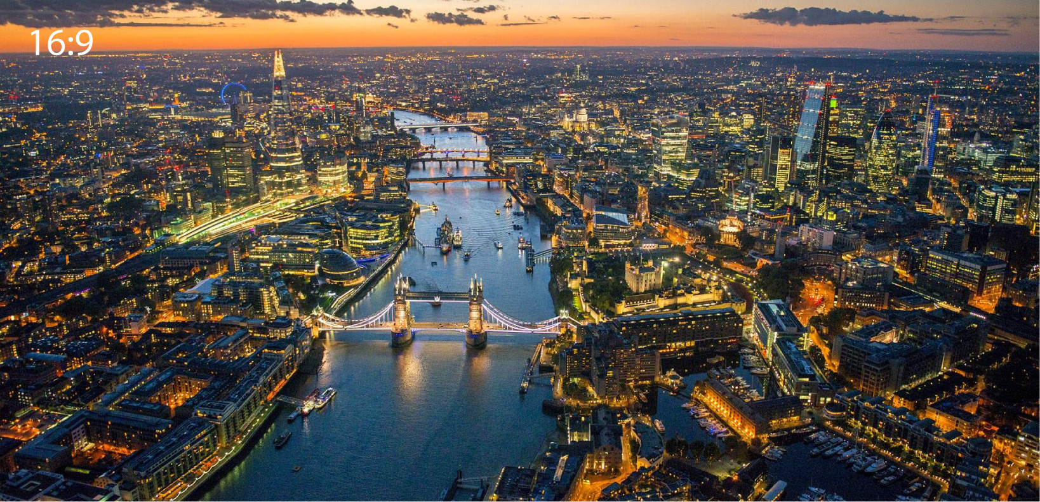
static/foto-16_9.jpg
