msgre/europe/static/img/brandenburg.jpg

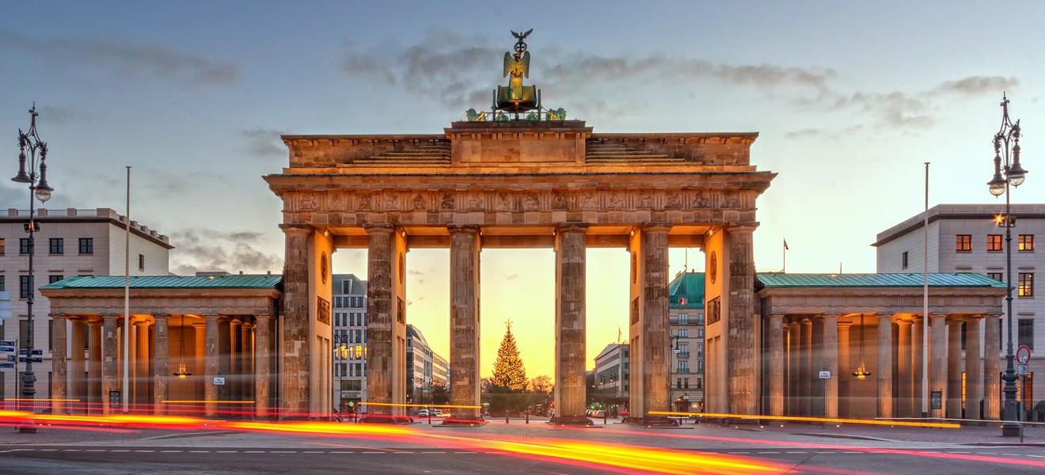
static/img/brandenburg.jpg
