msgre/europe/static/img/hraci_02.jpg

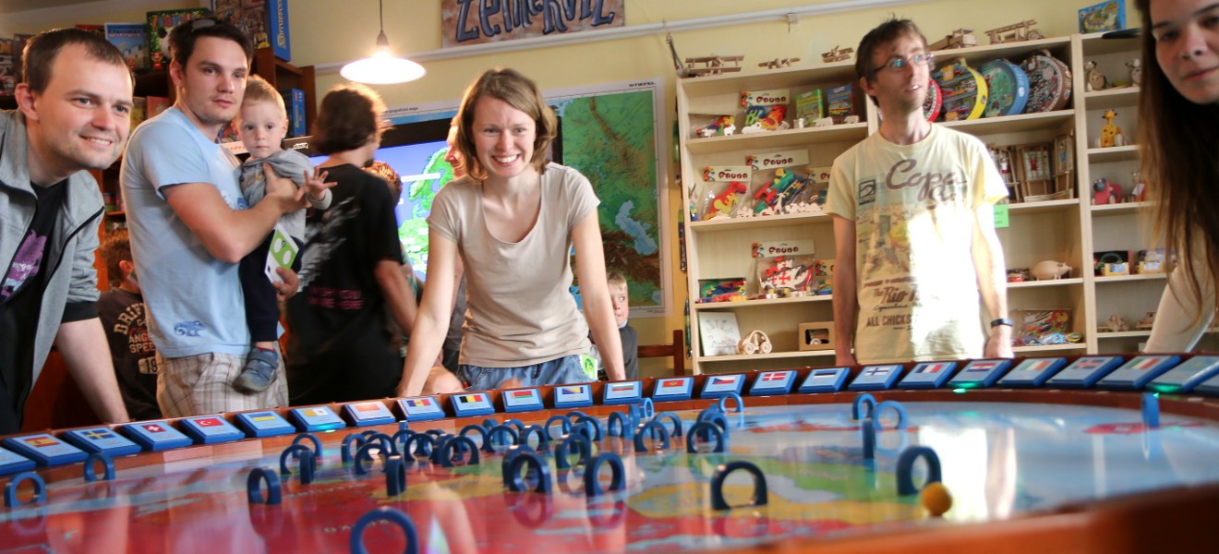
static/img/hraci_02.jpg
