msgre/europe/static/img/hraci_03.jpg

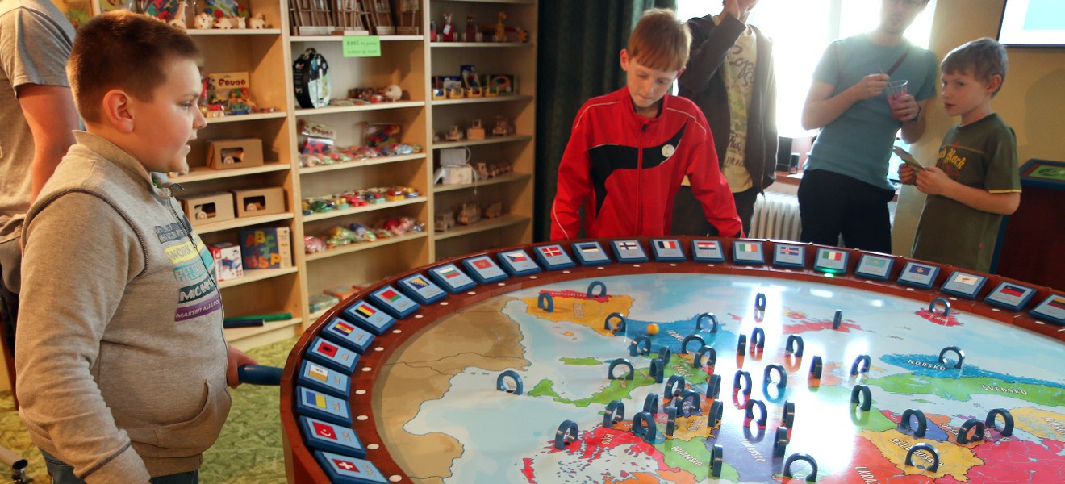
static/img/hraci_03.jpg
