msgre/europe/static/riga.jpg

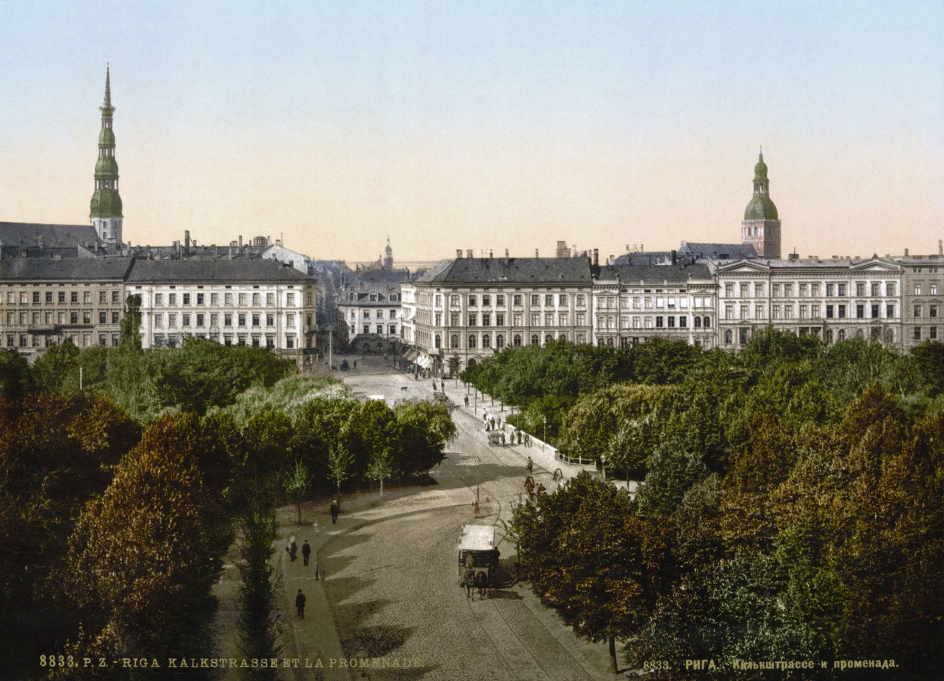
static/riga.jpg
