msgre/europe/static/vlajky.png

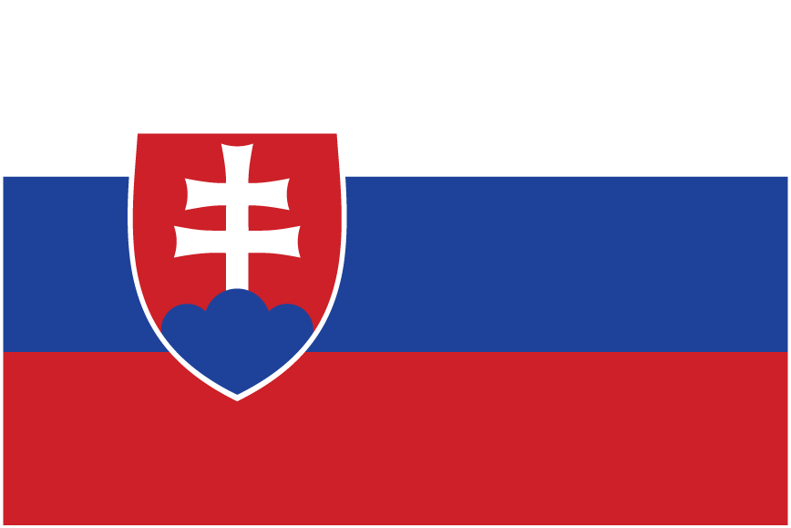
static/vlajky.png
