msgre/europe/hardware/neopixel/rs485.h

#ifndef __BL_RS485_H__
#define __BL_RS485_H__

#include <stdint.h>
#include <avr/pgmspace.h>

#define RS485_ERR -1

#define rs485_puthex4(val) do{rs485_puthex2(((uint16_t)(val))>>8);rs485_puthex2(((uint16_t)(val))&0xFF);}while(0)
#define rs485_puthex8(val) do{rs485_puthex4(((uint32_t)(val))>>16);rs485_puthex4(((uint32_t)(val))&0xFFFF);}while(0)

#define rs485_output() (RS485_DIR_PORT |= _BV(RS485_DIR_PIN))
#define rs485_input()  (RS485_DIR_PORT &= ~_BV(RS485_DIR_PIN))

void rs485_init(void);
void rs485_putc(char c);
void rs485_puts(char* s);
void rs485_putp(PGM_P s);
void rs485_puthex2(uint8_t val);

uint8_t rs485_available(void);
void rs485_flush(void);
int16_t rs485_getc(void);

#endif
