msgre/europe/europe/options/serializers.py

# -*- coding: utf-8 -*-

from rest_framework import serializers

from .models import Option


class OptionSerializer(serializers.ModelSerializer):
    class Meta:
        model = Option
        fields = ('key', 'value')
